yesnoj/FilMachine_Reworked/3D_Models/FilMachine_macchina_v5/png/bagno_e_idraulica.png

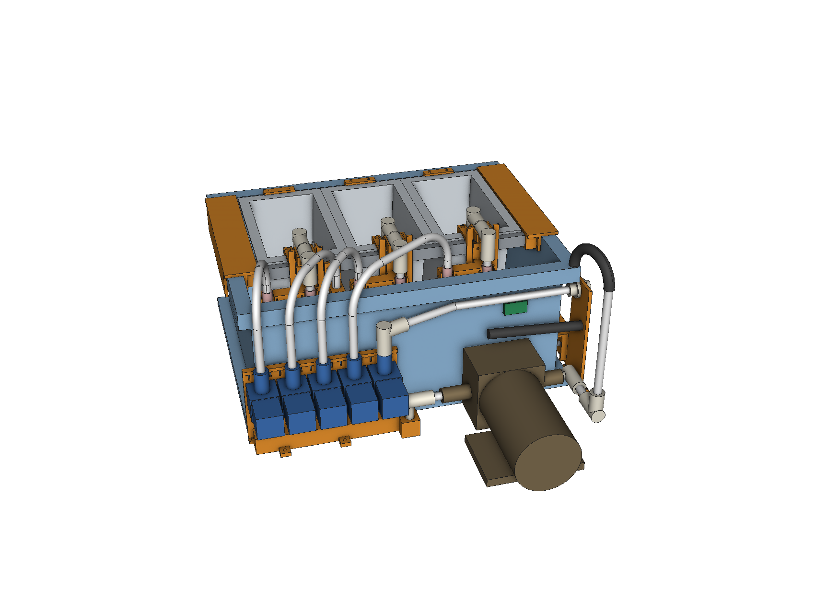
3D_Models/FilMachine_macchina_v5/png/bagno_e_idraulica.png
