yesnoj/FilMachine_Reworked/3D_Models/FilMachine_macchina_v5/png/culla_universale_135.png

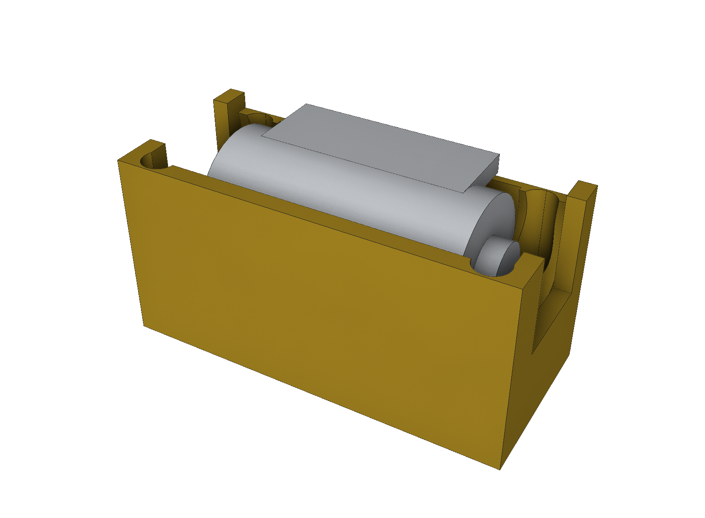
3D_Models/FilMachine_macchina_v5/png/culla_universale_135.png
