yesnoj/FilMachine_Reworked/3D_Models/FilMachine_macchina_v5/png/sez_macchina_tank.png

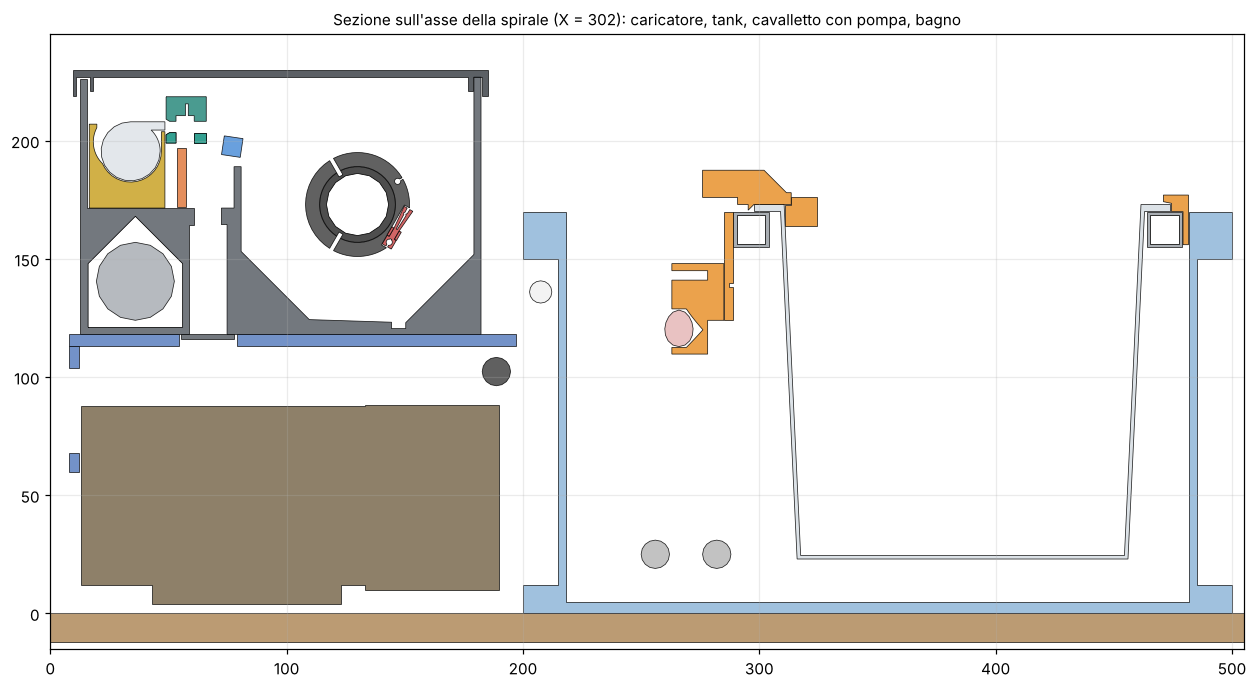
3D_Models/FilMachine_macchina_v5/png/sez_macchina_tank.png
