yesnoj/FilMachine_Reworked/3D_Models/FilMachine_macchina_v5/png/tank_trasmissione.png

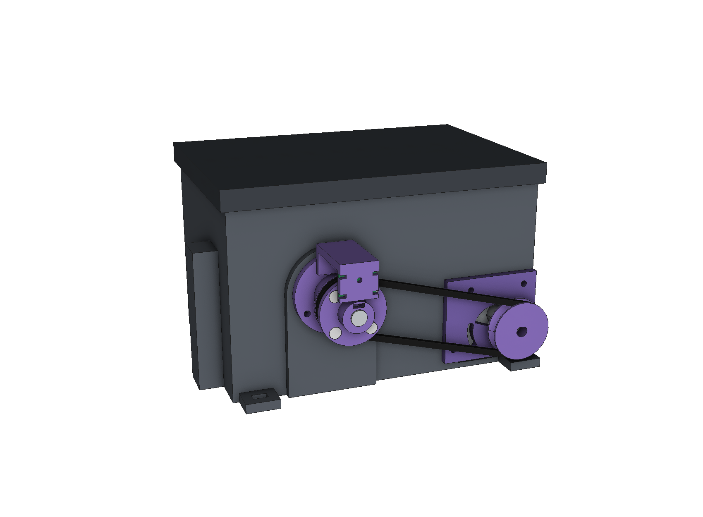
3D_Models/FilMachine_macchina_v5/png/tank_trasmissione.png
