yesnoj/FilMachine_Reworked/3D_Models/FilMachine_macchina_v5/step/B01_corpo_tank.step

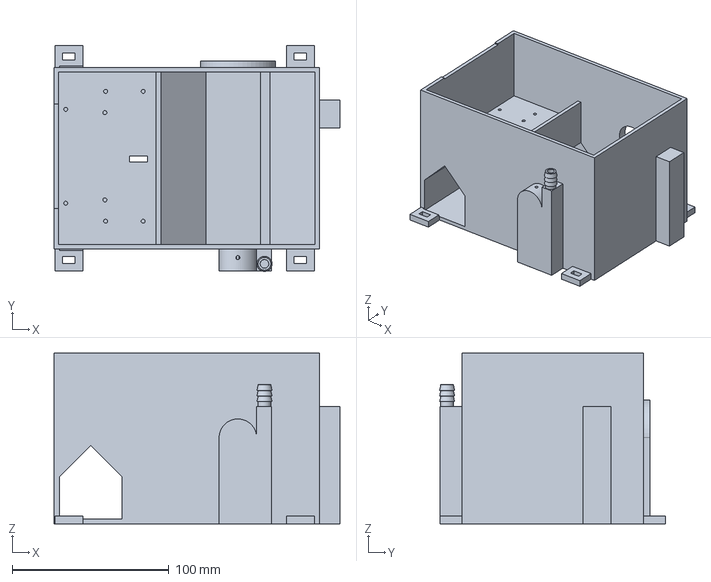
[picture p39: CAD file, 2026-10-09]
3D_Models/FilMachine_macchina_v5/step/B01_corpo_tank.step
182.8 x 144.3 x 109.0 mm
