yesnoj/FilMachine_Reworked/3D_Models/FilMachine_macchina_v5/step/B22_puleggia_motore.step

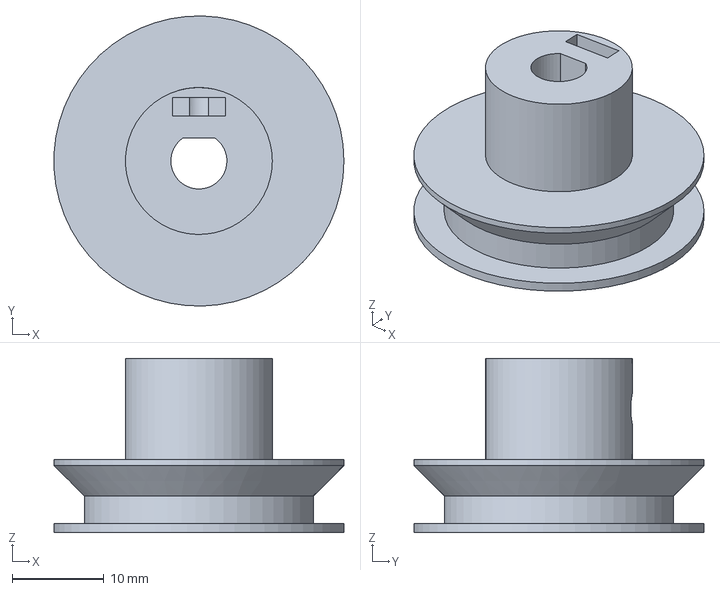
[picture p41: CAD file, 2026-10-09]
3D_Models/FilMachine_macchina_v5/step/B22_puleggia_motore.step
31.6 x 31.6 x 19.0 mm
