yesnoj/FilMachine_Reworked/3D_Models/FilMachine_macchina_v5/step/D11_paratia_posteriore.step

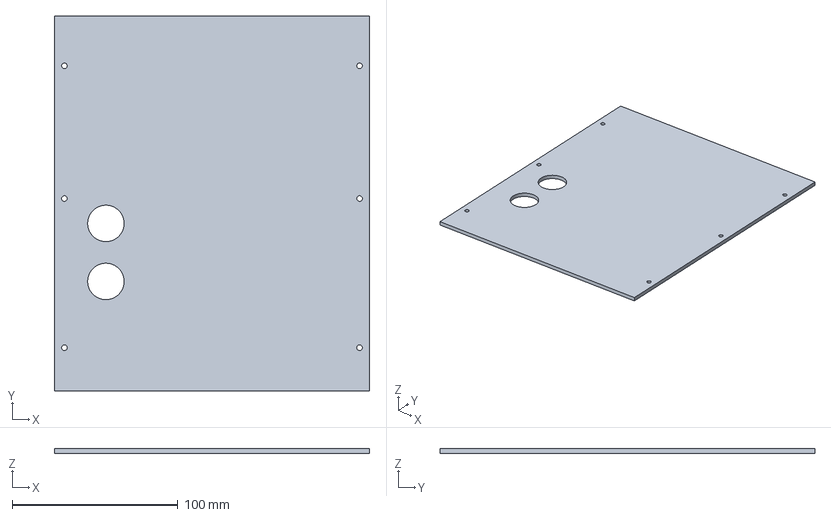
[picture p42: CAD file, 2026-10-09]
3D_Models/FilMachine_macchina_v5/step/D11_paratia_posteriore.step
190.0 x 226.0 x 3.00 mm
