yesnoj/FilMachine_Reworked/3D_Models/FilMachine_macchina_v5/step/D01_piano_cavalletto.step

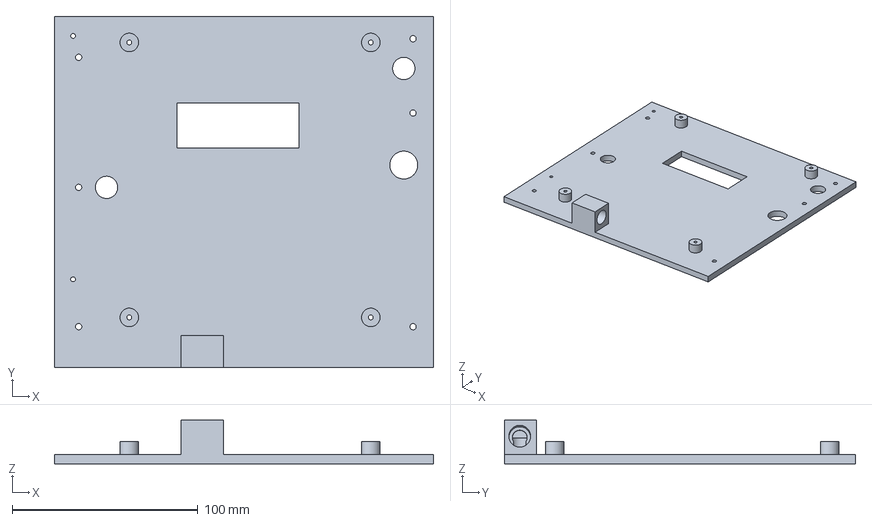
[picture p43: CAD file, 2026-10-09]
3D_Models/FilMachine_macchina_v5/step/D01_piano_cavalletto.step
204.0 x 189.0 x 23.5 mm
