yesnoj/FilMachine_Reworked/3D_Models/FilMachine_macchina_v5/step/A08_clip_cursore.step

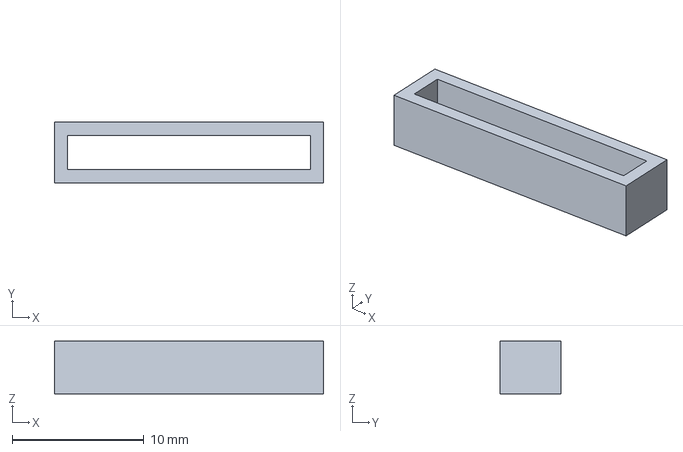
[picture p44: CAD file, 2026-10-09]
3D_Models/FilMachine_macchina_v5/step/A08_clip_cursore.step
20.4 x 4.60 x 4.00 mm
