yesnoj/FilMachine_Reworked/3D_Models/FilMachine_macchina_v5/step/C01_sella_testina.step

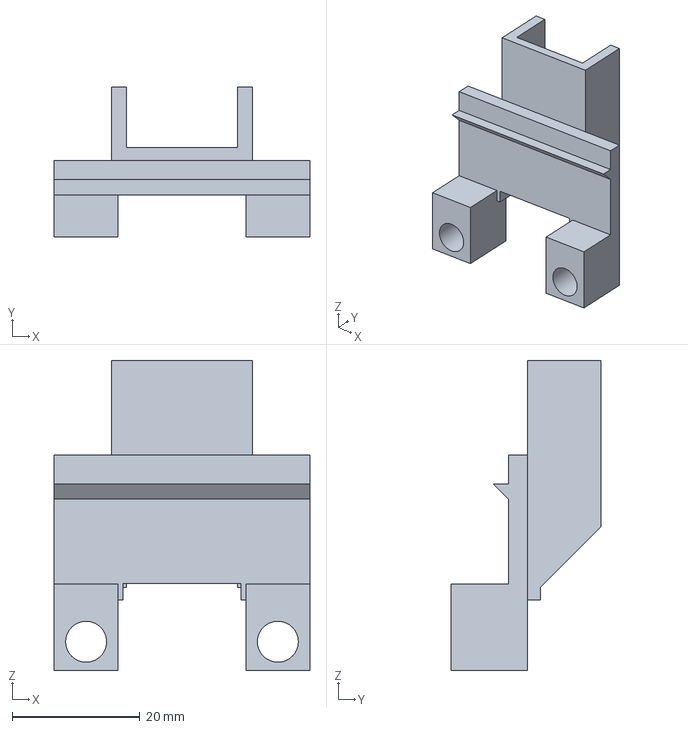
[picture p45: CAD file, 2026-10-09]
3D_Models/FilMachine_macchina_v5/step/C01_sella_testina.step
40.0 x 23.5 x 48.5 mm
