yesnoj/FilMachine_Reworked/3D_Models/FilMachine_macchina_v5/step/D14_colonnina_alta.step

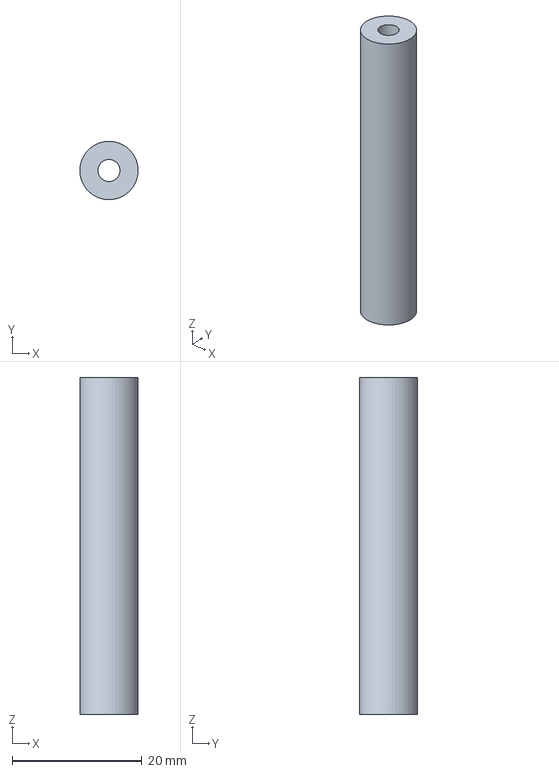
[picture p46: CAD file, 2026-10-09]
3D_Models/FilMachine_macchina_v5/step/D14_colonnina_alta.step
8.99 x 9.00 x 52.0 mm
