yesnoj/FilMachine_Reworked/3D_Models/FilMachine_macchina_v5/step/D03_fianco_cavalletto_DX.step

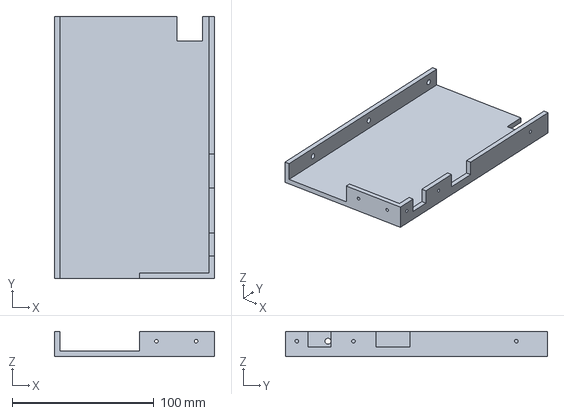
[picture p47: CAD file, 2026-10-09]
3D_Models/FilMachine_macchina_v5/step/D03_fianco_cavalletto_DX.step
113.0 x 185.0 x 18.0 mm
