yesnoj/FilMachine_Reworked/3D_Models/FilMachine_macchina_v5/step/B25_staffa_hall.step

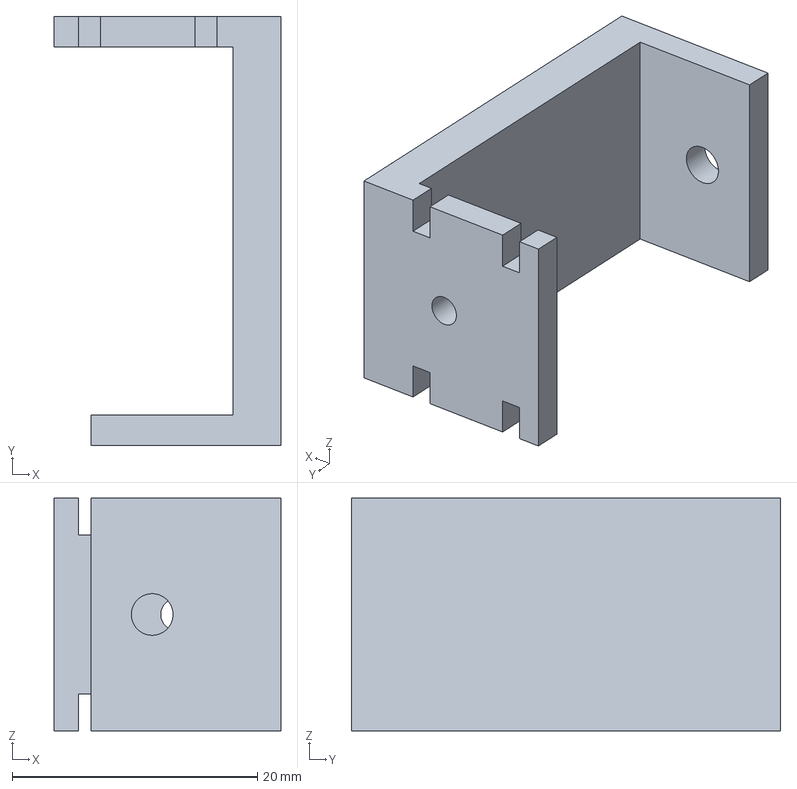
[picture p48: CAD file, 2026-10-09]
3D_Models/FilMachine_macchina_v5/step/B25_staffa_hall.step
18.5 x 35.0 x 19.0 mm
