yesnoj/FilMachine_Reworked/3D_Models/FilMachine_macchina_v5/step/A07_clip_ganascia.step

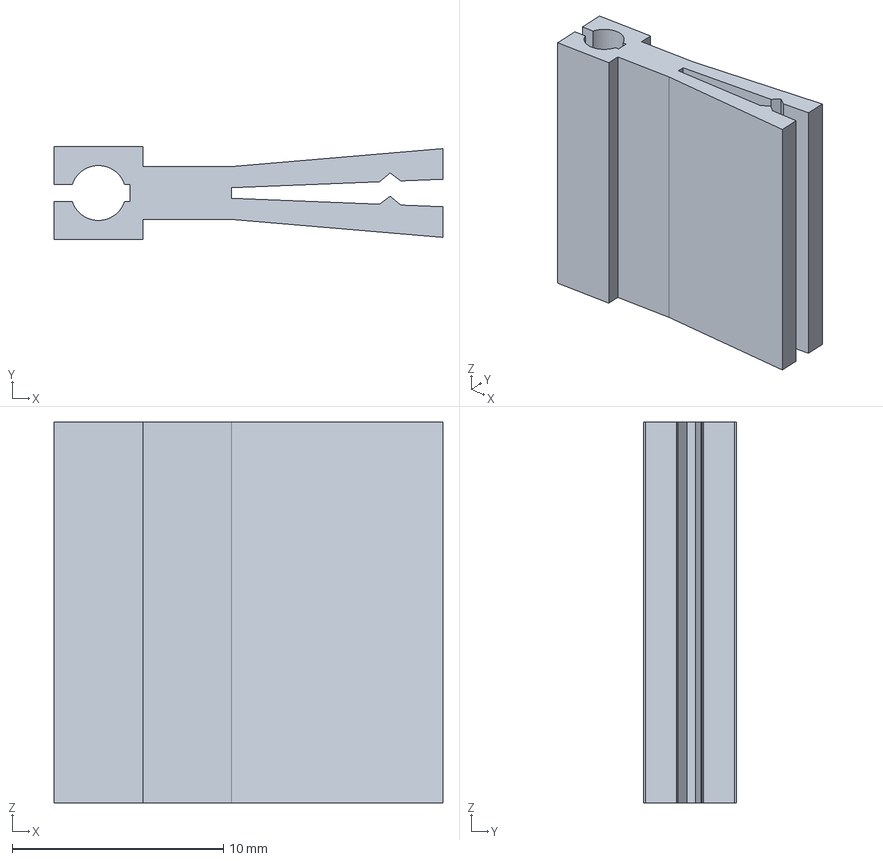
[picture p49: CAD file, 2026-10-09]
3D_Models/FilMachine_macchina_v5/step/A07_clip_ganascia.step
18.4 x 4.40 x 18.0 mm
