yesnoj/FilMachine_Reworked/3D_Models/FilMachine_macchina_v5/step/C02_culla_sifone.step

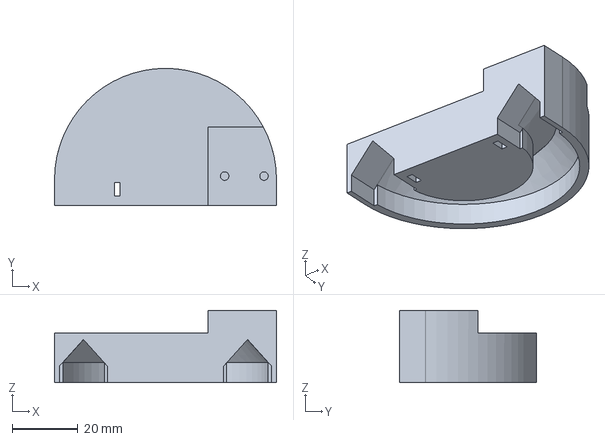
[picture p50: CAD file, 2026-10-09]
3D_Models/FilMachine_macchina_v5/step/C02_culla_sifone.step
67.6 x 41.8 x 22.0 mm
