yesnoj/FilMachine_Reworked/3D_Models/FilMachine_macchina_v5/step/B08_morsetto_lama_DX.step

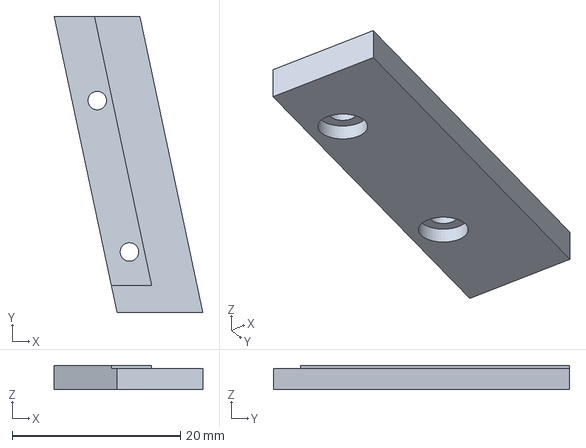
[picture p51: CAD file, 2026-10-09]
3D_Models/FilMachine_macchina_v5/step/B08_morsetto_lama_DX.step
17.7 x 35.2 x 2.88 mm
