yesnoj/FilMachine_Reworked/3D_Models/FilMachine_macchina_v5/step/D04_frontale_cavalletto.step

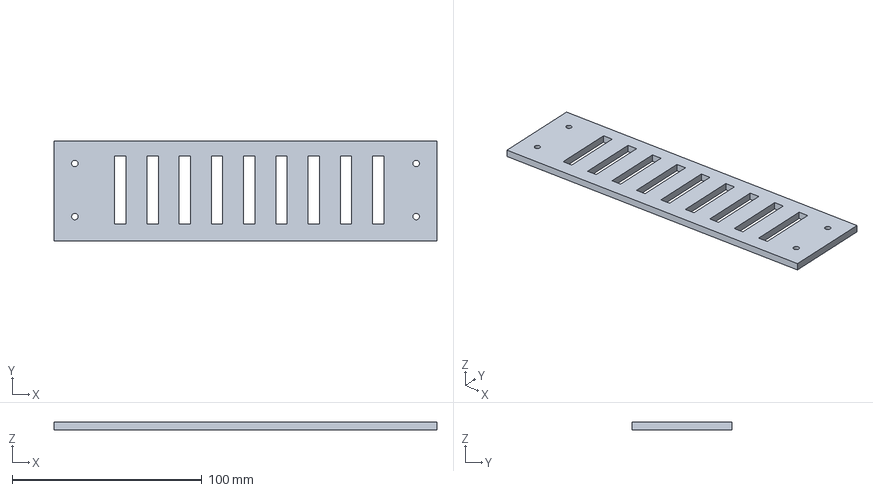
[picture p52: CAD file, 2026-10-09]
3D_Models/FilMachine_macchina_v5/step/D04_frontale_cavalletto.step
202.0 x 53.0 x 4.00 mm
