yesnoj/FilMachine_Reworked/3D_Models/FilMachine_macchina_v5/step/B24_perno_folle.step

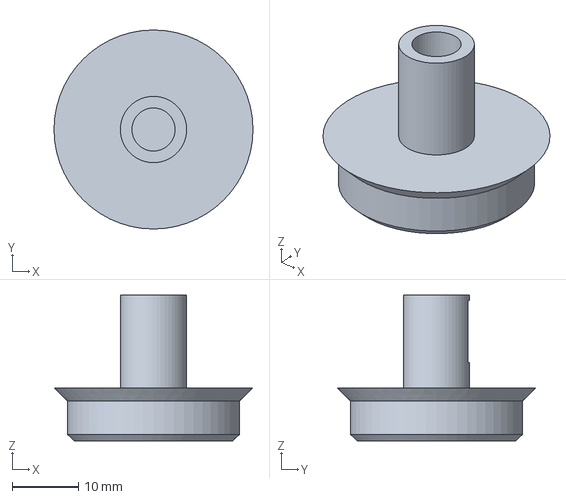
[picture p53: CAD file, 2026-10-09]
3D_Models/FilMachine_macchina_v5/step/B24_perno_folle.step
30.0 x 30.0 x 22.0 mm
