yesnoj/FilMachine_Reworked/3D_Models/FilMachine_macchina_v5/step/B18_distanziale_paraolio.step

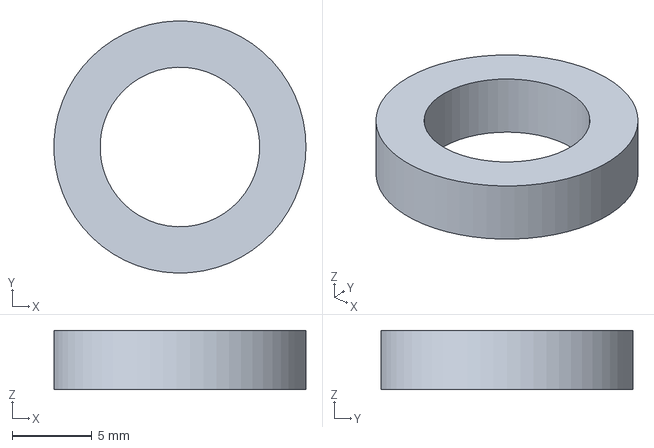
[picture p54: CAD file, 2026-10-09]
3D_Models/FilMachine_macchina_v5/step/B18_distanziale_paraolio.step
15.8 x 15.8 x 3.70 mm
