yesnoj/FilMachine_Reworked/3D_Models/FilMachine_macchina_v5/step/B17_cartuccia_cuscinetti.step

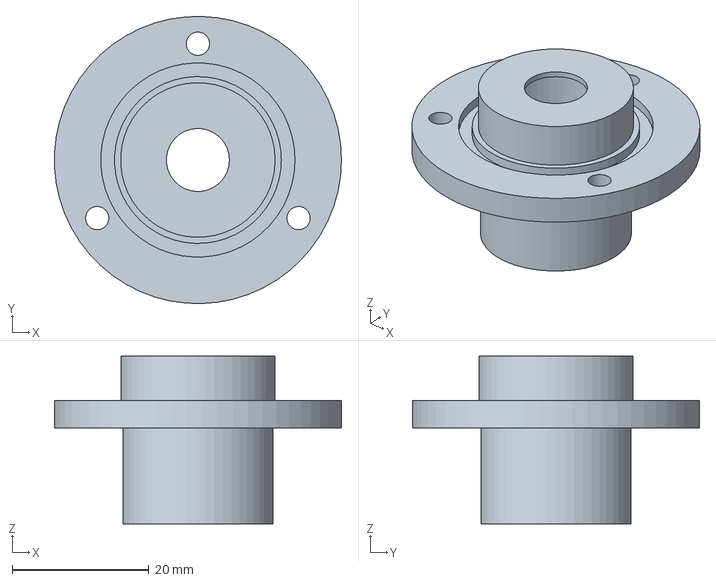
[picture p55: CAD file, 2026-10-09]
3D_Models/FilMachine_macchina_v5/step/B17_cartuccia_cuscinetti.step
42.0 x 42.0 x 24.5 mm
