yesnoj/FilMachine_Reworked/3D_Models/FilMachine_macchina_v5/step/B16_trascinatore.step

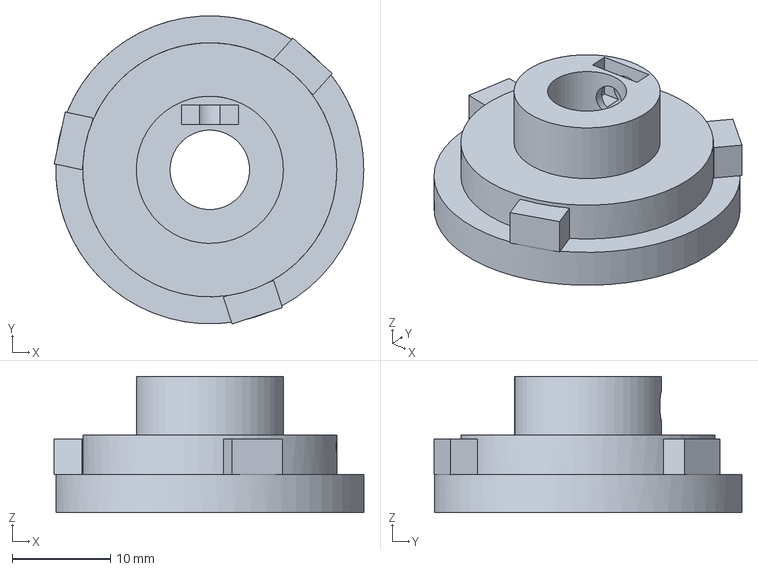
[picture p56: CAD file, 2026-10-09]
3D_Models/FilMachine_macchina_v5/step/B16_trascinatore.step
31.6 x 31.4 x 13.9 mm
