yesnoj/FilMachine_Reworked/3D_Models/FilMachine_macchina_v5/step/B23_piastra_motore.step

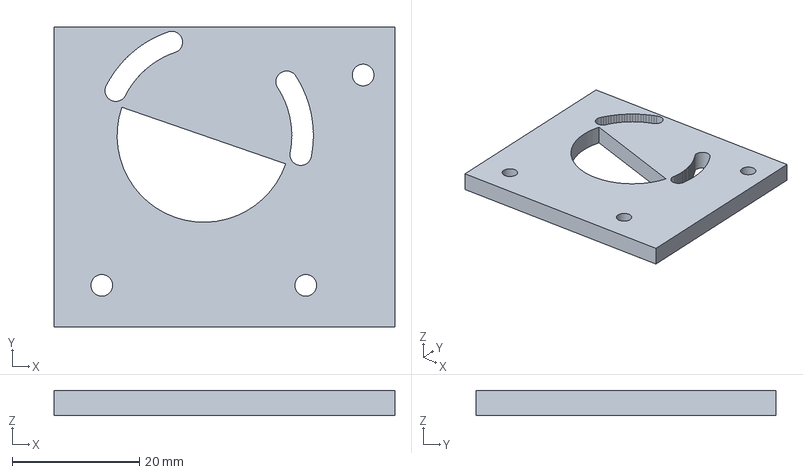
[picture p57: CAD file, 2026-10-09]
3D_Models/FilMachine_macchina_v5/step/B23_piastra_motore.step
53.5 x 47.0 x 4.00 mm
