yesnoj/FilMachine_Reworked/3D_Models/FilMachine_macchina_v5/step/B03_coperchietto_vano_servo.step

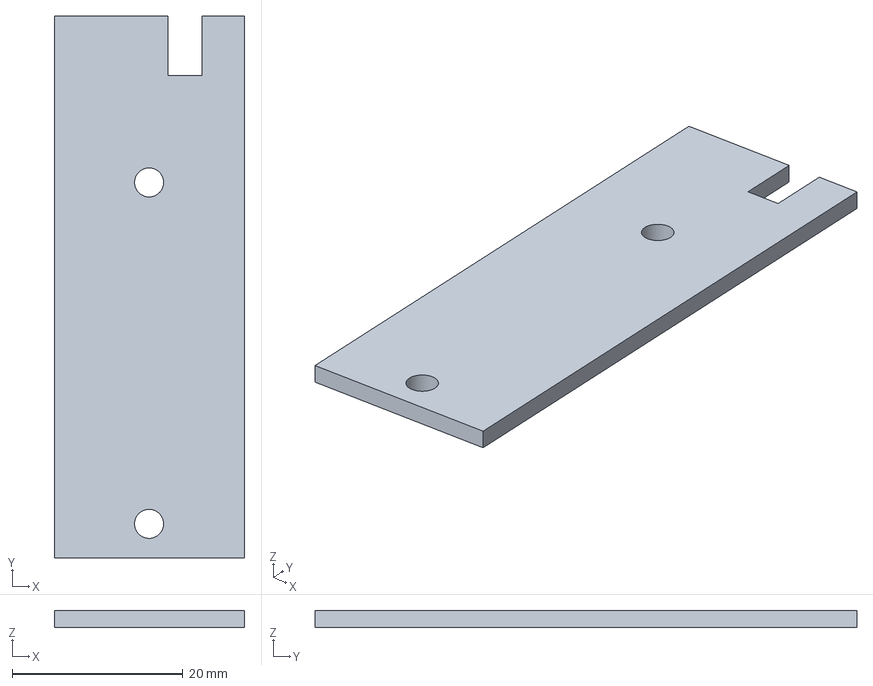
[picture p58: CAD file, 2026-10-09]
3D_Models/FilMachine_macchina_v5/step/B03_coperchietto_vano_servo.step
22.3 x 63.5 x 2.00 mm
