yesnoj/FilMachine_Reworked/3D_Models/FilMachine_macchina_v5/step/B13_barra_guida.step

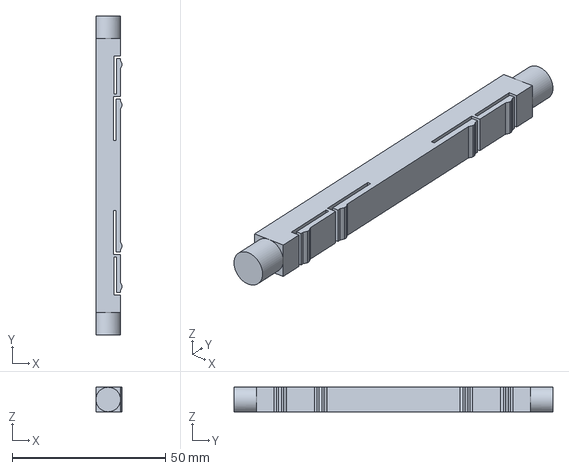
[picture p59: CAD file, 2026-10-09]
3D_Models/FilMachine_macchina_v5/step/B13_barra_guida.step
8.50 x 104.0 x 8.00 mm
