yesnoj/FilMachine_Reworked/3D_Models/FilMachine_macchina_v5/step/A04_tamburo.step

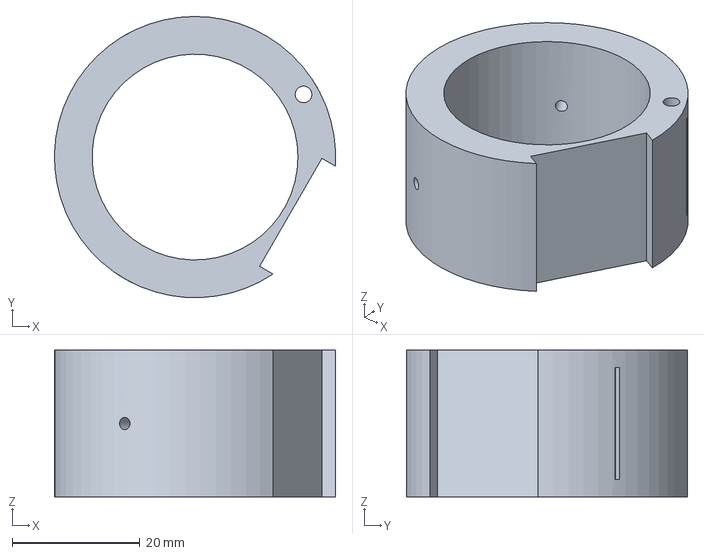
[picture p60: CAD file, 2026-10-09]
3D_Models/FilMachine_macchina_v5/step/A04_tamburo.step
44.0 x 44.0 x 23.0 mm
