yesnoj/FilMachine_Reworked/3D_Models/FilMachine_macchina_v5/step/B15_slitta_SX.step

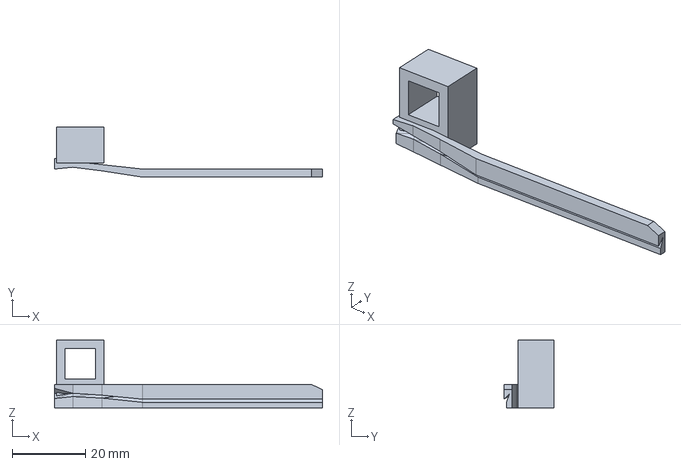
[picture p61: CAD file, 2026-10-09]
3D_Models/FilMachine_macchina_v5/step/B15_slitta_SX.step
73.0 x 13.7 x 18.5 mm
