yesnoj/FilMachine_Reworked/3D_Models/FilMachine_macchina_v5/step/B12_culla_universale.step

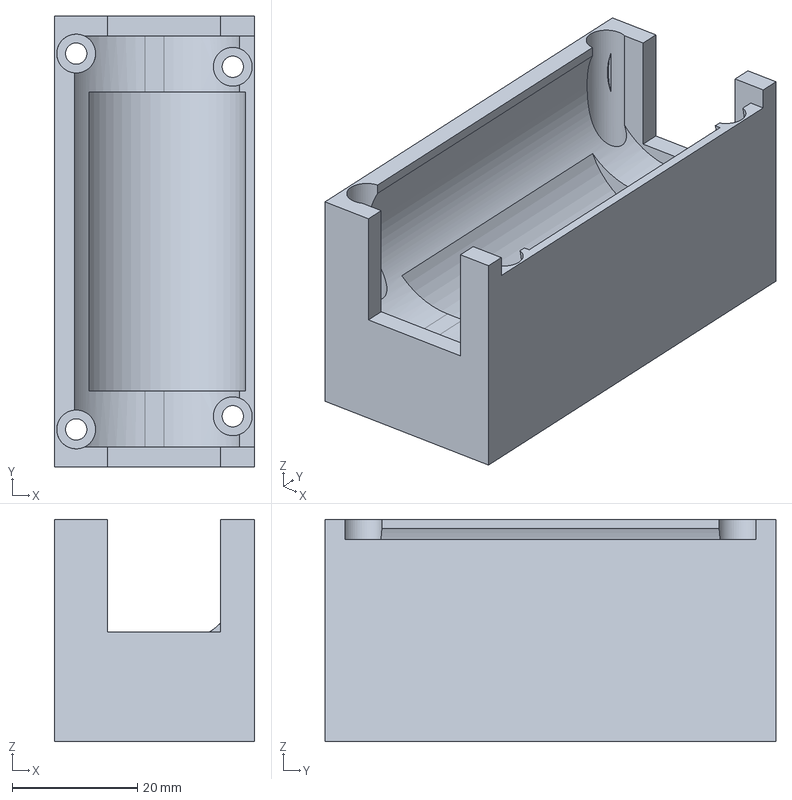
[picture p62: CAD file, 2026-10-09]
3D_Models/FilMachine_macchina_v5/step/B12_culla_universale.step
32.0 x 72.0 x 35.5 mm
