yesnoj/FilMachine_Reworked/3D_Models/FilMachine_macchina_v5/step/B19_distanziale_cuscinetti.step

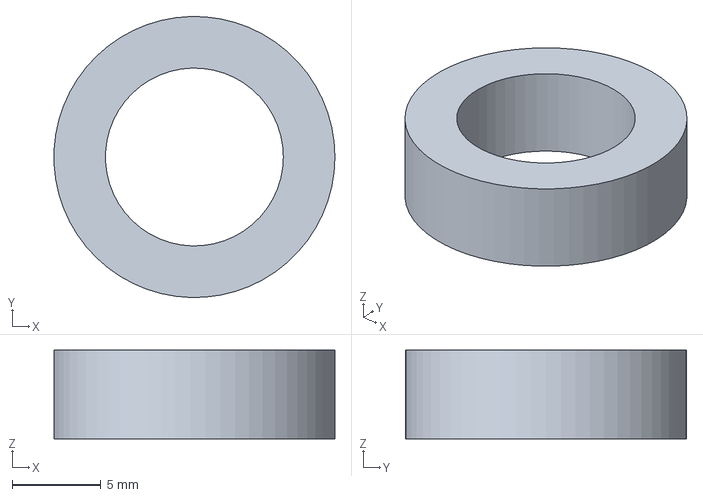
[picture p63: CAD file, 2026-10-09]
3D_Models/FilMachine_macchina_v5/step/B19_distanziale_cuscinetti.step
15.8 x 15.8 x 5.00 mm
