yesnoj/FilMachine_Reworked/3D_Models/FilMachine_macchina_v5/step/D12_ripiano_griglia.step

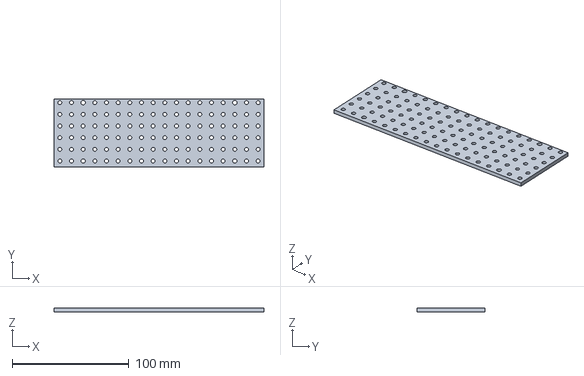
[picture p64: CAD file, 2026-10-09]
3D_Models/FilMachine_macchina_v5/step/D12_ripiano_griglia.step
180.0 x 58.0 x 3.00 mm
