yesnoj/FilMachine_Reworked/3D_Models/FilMachine_macchina_v5/step/C06_portasonde.step

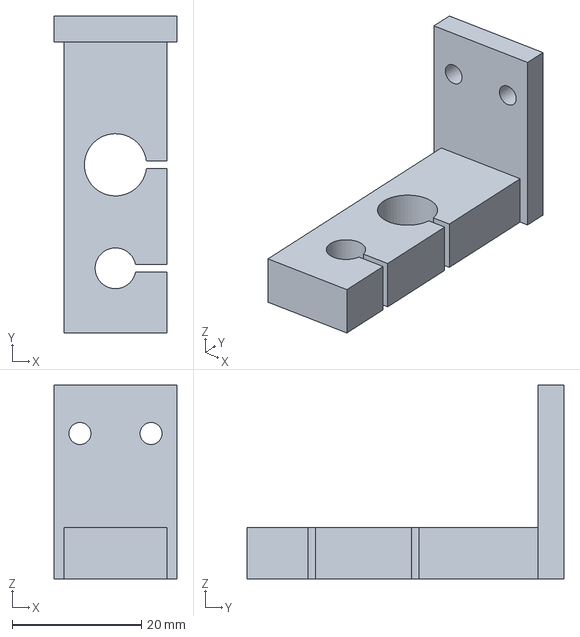
[picture p65: CAD file, 2026-10-09]
3D_Models/FilMachine_macchina_v5/step/C06_portasonde.step
19.0 x 49.0 x 30.0 mm
