yesnoj/FilMachine_Reworked/3D_Models/FilMachine_macchina_v5/step/B20_rasamento_puleggia.step

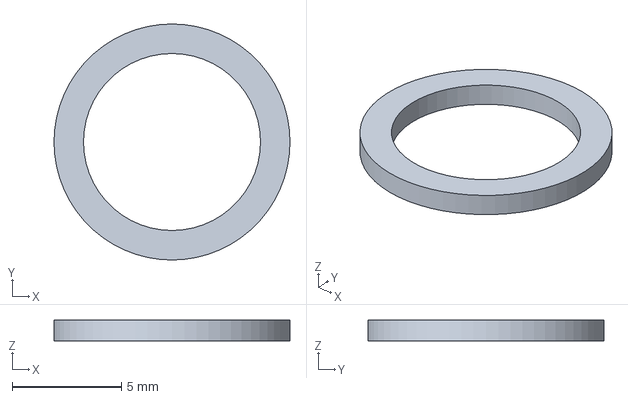
[picture p66: CAD file, 2026-10-09]
3D_Models/FilMachine_macchina_v5/step/B20_rasamento_puleggia.step
10.8 x 10.8 x 0.95 mm
