yesnoj/FilMachine_Reworked/3D_Models/FilMachine_macchina_v5/step/D07_fianco_elettronica_DX.step

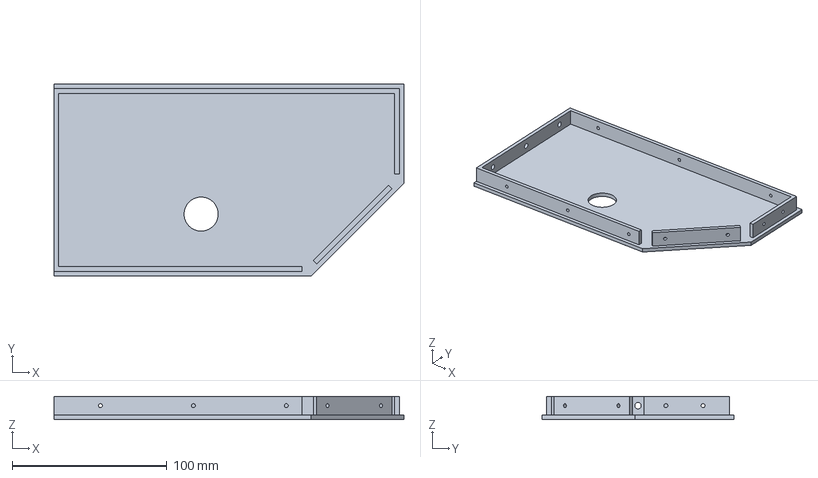
[picture p67: CAD file, 2026-10-09]
3D_Models/FilMachine_macchina_v5/step/D07_fianco_elettronica_DX.step
226.0 x 124.0 x 15.0 mm
