yesnoj/FilMachine_Reworked/3D_Models/FilMachine_macchina_v5/step/C09_staffa_scarichi.step

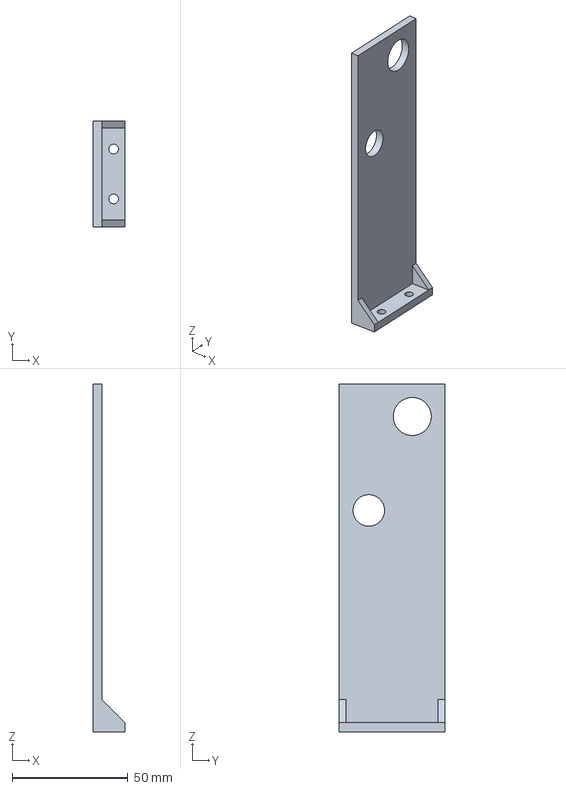
[picture p68: CAD file, 2026-10-09]
3D_Models/FilMachine_macchina_v5/step/C09_staffa_scarichi.step
14.0 x 45.5 x 150.0 mm
