yesnoj/FilMachine_Reworked/3D_Models/FilMachine_macchina_v5/step/C07_collettore.step

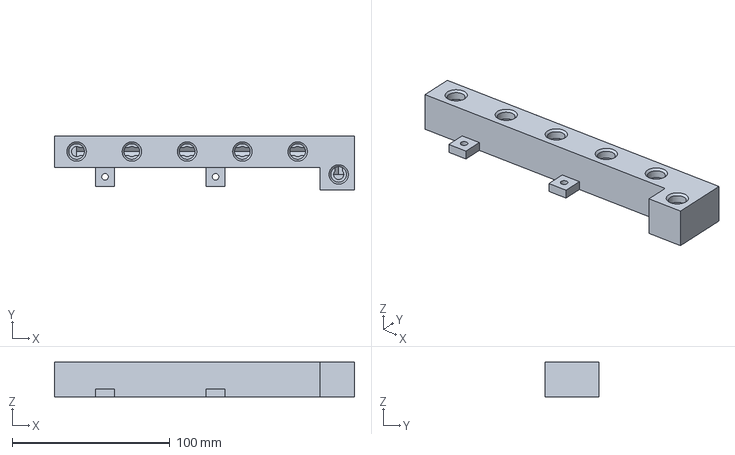
[picture p69: CAD file, 2026-10-09]
3D_Models/FilMachine_macchina_v5/step/C07_collettore.step
190.0 x 34.5 x 22.0 mm
