yesnoj/FilMachine_Reworked/3D_Models/FilMachine_macchina_v5/step/D13_colonnina_bassa.step

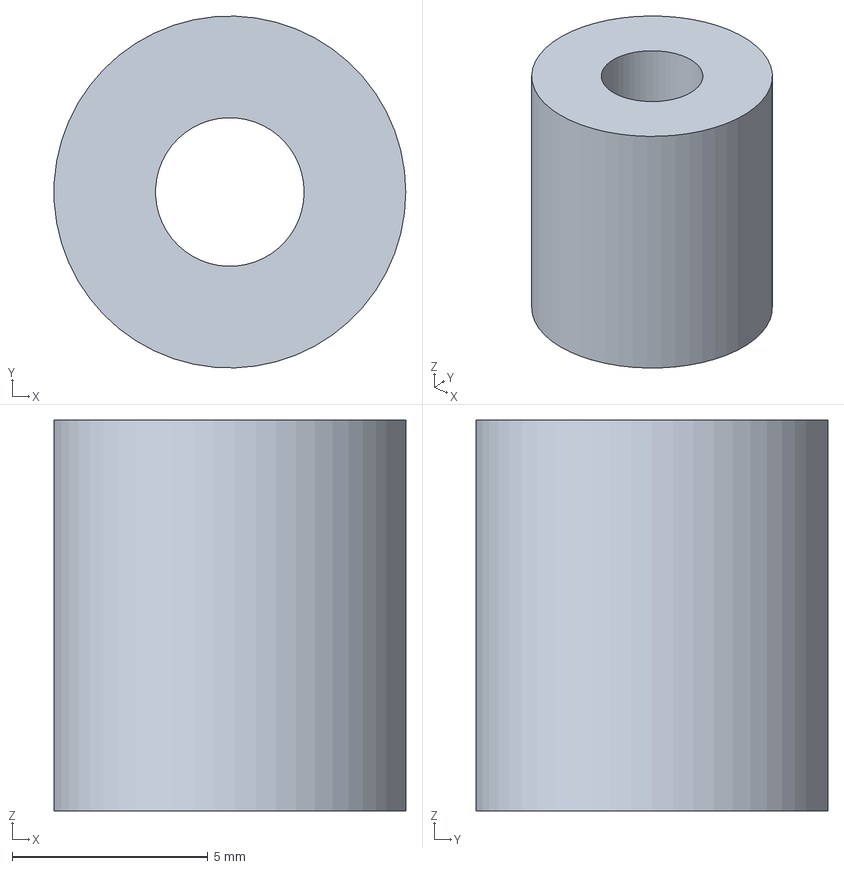
[picture p70: CAD file, 2026-10-09]
3D_Models/FilMachine_macchina_v5/step/D13_colonnina_bassa.step
8.99 x 9.00 x 10.0 mm
