yesnoj/FilMachine_Reworked/3D_Models/FilMachine_macchina_v5/step/D15_morsetto_scheda.step

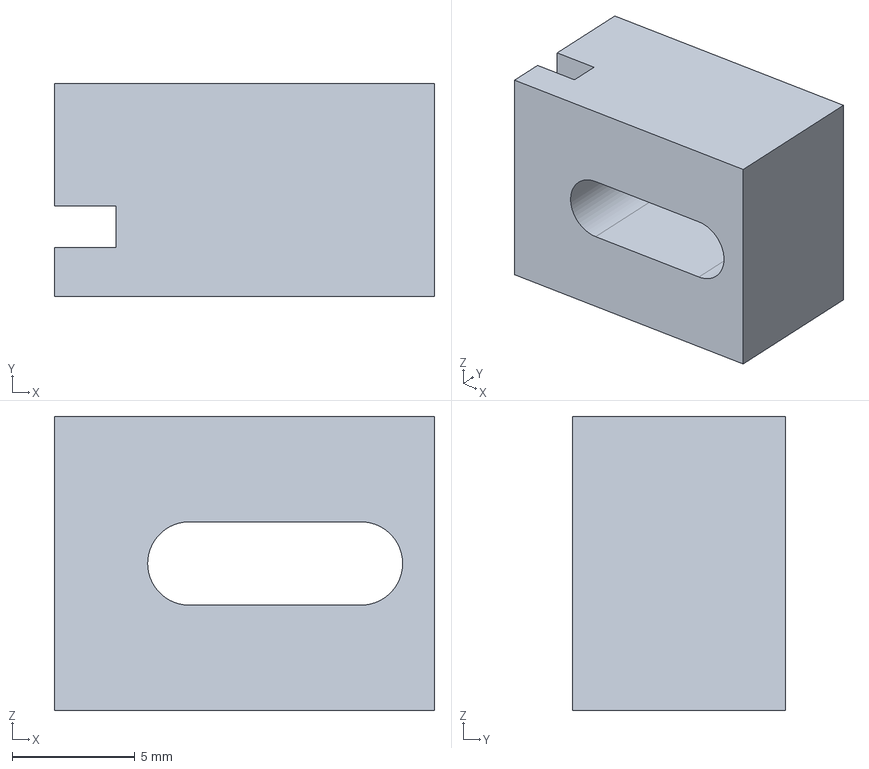
[picture p71: CAD file, 2026-10-09]
3D_Models/FilMachine_macchina_v5/step/D15_morsetto_scheda.step
15.5 x 8.70 x 12.0 mm
