yesnoj/FilMachine_Reworked/3D_Models/FilMachine_macchina_v5/step/C04_fermo_posteriore.step

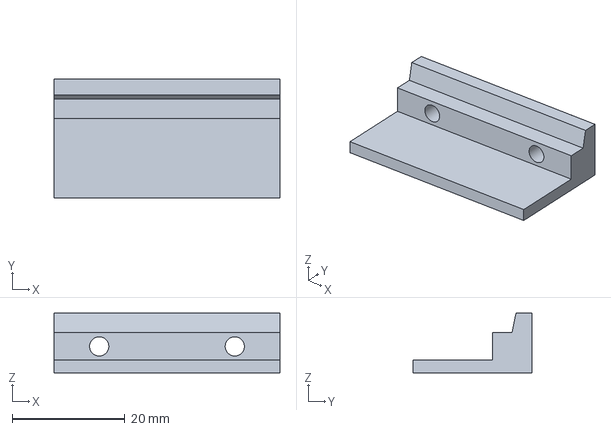
[picture p72: CAD file, 2026-10-09]
3D_Models/FilMachine_macchina_v5/step/C04_fermo_posteriore.step
40.0 x 21.0 x 10.6 mm
