yesnoj/FilMachine_Reworked/3D_Models/FilMachine_macchina_v5/step/C08_pettine_valvole.step

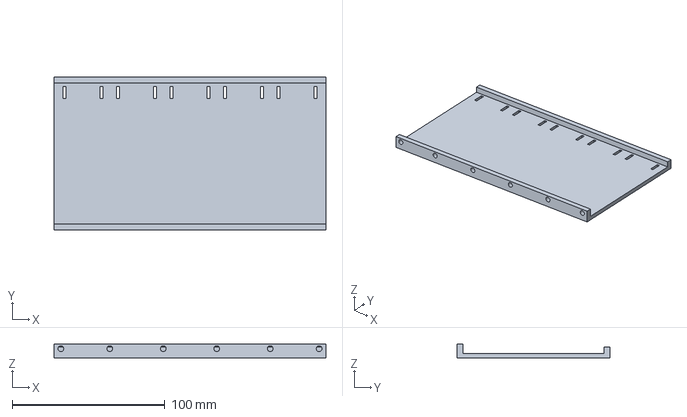
[picture p73: CAD file, 2026-10-09]
3D_Models/FilMachine_macchina_v5/step/C08_pettine_valvole.step
178.0 x 100.0 x 9.10 mm
