yesnoj/FilMachine_Reworked/3D_Models/FilMachine_macchina_v5/step/D17_linguetta_display.step

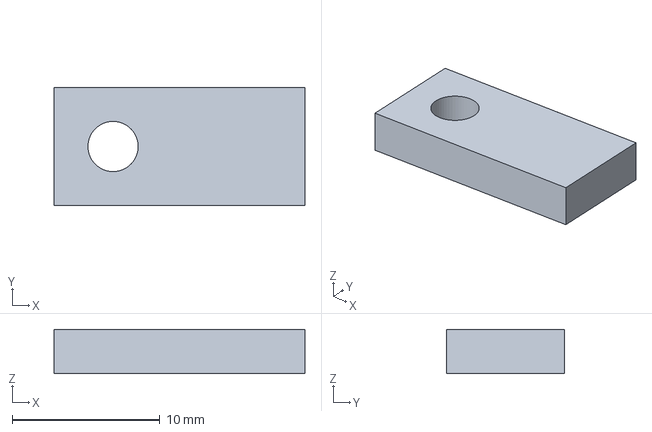
[picture p74: CAD file, 2026-10-09]
3D_Models/FilMachine_macchina_v5/step/D17_linguetta_display.step
17.0 x 8.00 x 3.00 mm
