yesnoj/FilMachine_Reworked/3D_Models/FilMachine_macchina_v5/step/A09_provino_accoppiamento.step

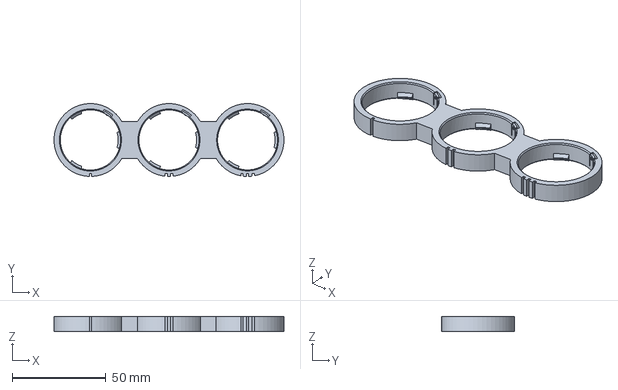
[picture p75: CAD file, 2026-10-09]
3D_Models/FilMachine_macchina_v5/step/A09_provino_accoppiamento.step
123.0 x 39.0 x 8.00 mm
