yesnoj/FilMachine_Reworked/3D_Models/FilMachine_macchina_v5/step/C03_staffa_ganci.step

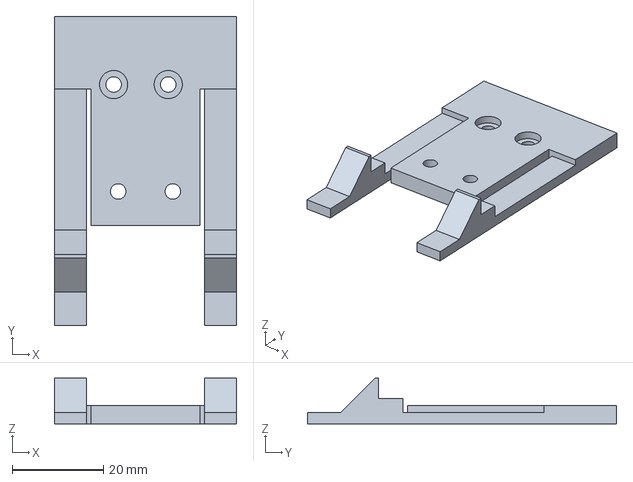
[picture p76: CAD file, 2026-10-09]
3D_Models/FilMachine_macchina_v5/step/C03_staffa_ganci.step
40.0 x 68.0 x 10.0 mm
