yesnoj/FilMachine_Reworked/3D_Models/FilMachine_macchina_v5/step/D09_plancia_display.step

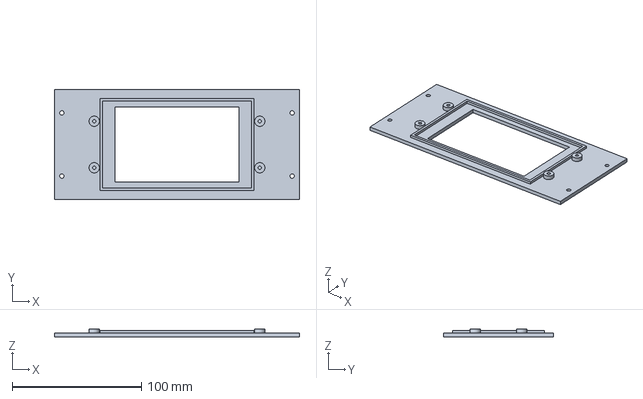
[picture p77: CAD file, 2026-10-09]
3D_Models/FilMachine_macchina_v5/step/D09_plancia_display.step
189.4 x 84.9 x 6.20 mm
