yesnoj/FilMachine_Reworked/3D_Models/FilMachine_macchina_v5/step/B21_puleggia_spirale.step

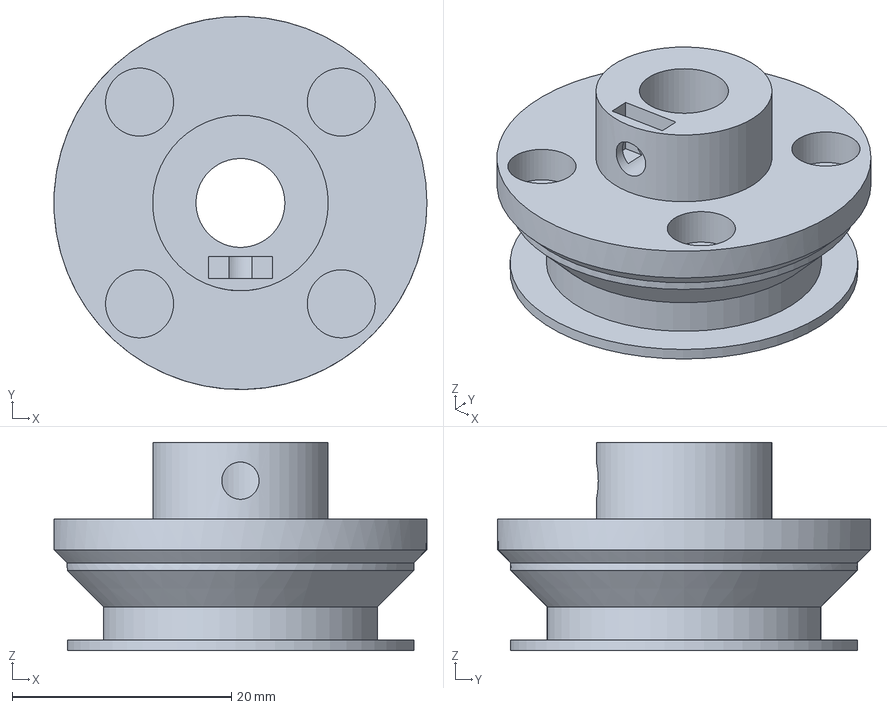
[picture p78: CAD file, 2026-10-09]
3D_Models/FilMachine_macchina_v5/step/B21_puleggia_spirale.step
34.0 x 34.0 x 19.0 mm
