yesnoj/FilMachine_Reworked/3D_Models/FilMachine_macchina_v5/step/B10_biella.step

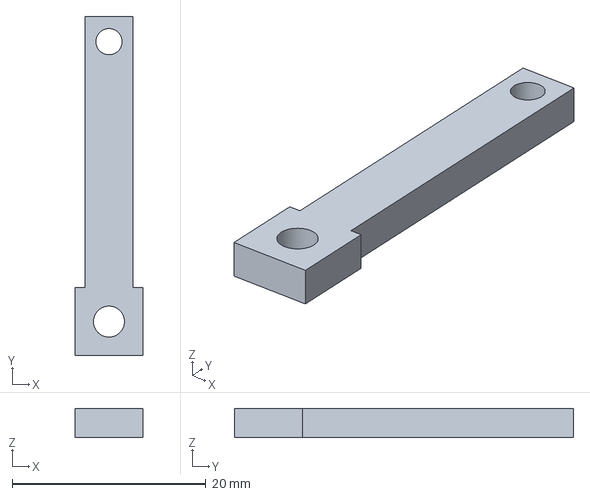
[picture p79: CAD file, 2026-10-09]
3D_Models/FilMachine_macchina_v5/step/B10_biella.step
7.00 x 35.0 x 3.00 mm
