yesnoj/FilMachine_Reworked/3D_Models/FilMachine_macchina_v5/step/D10_tetto_elettronica.step

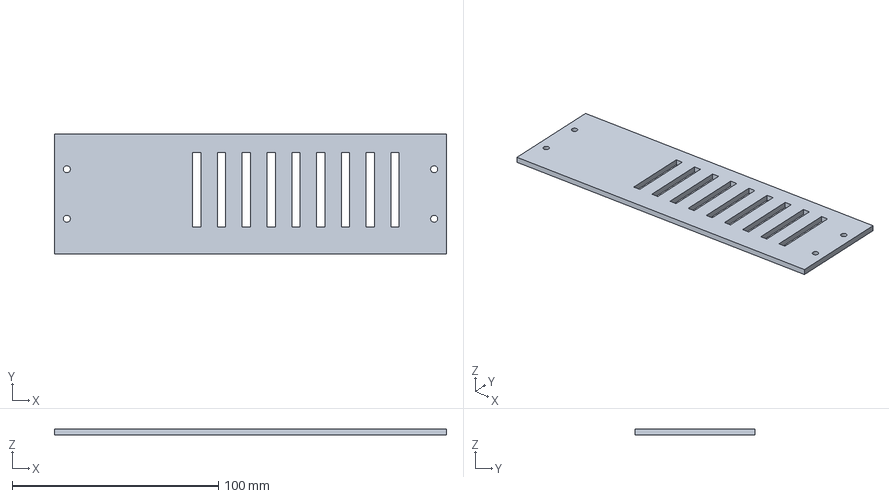
[picture p80: CAD file, 2026-10-09]
3D_Models/FilMachine_macchina_v5/step/D10_tetto_elettronica.step
190.0 x 58.0 x 3.00 mm
