yesnoj/FilMachine_Reworked/hardware/FilMachine_Breakout_v1/FilMachine_Breakout_v1.kicad_sch

## KiCad design hardware/FilMachine_Breakout_v1/FilMachine_Breakout_v1.kicad_sch (2026-05-02)

Schematic: FilMachine_Breakout_v1.kicad_sch

Parts:
C1, C2: 100nF; C_0805_2012Metric
J1: J9_Expand_IO_2x13; PinHeader_2x13_P2.54mm_Vertical
J2: MOTOR_3P_5.08mm; TerminalBlock_bornier-3_P5.08mm
J3: TEMP_3P_5.08mm; TerminalBlock_bornier-3_P5.08mm
J4: FLOW_3P_5.08mm; TerminalBlock_bornier-3_P5.08mm
J5: I2C_4P_5.08mm; TerminalBlock_bornier-4_P5.08mm
J6: WATER_4P_5.08mm; TerminalBlock_bornier-4_P5.08mm
J7: HALL_3P_5.08mm; TerminalBlock_bornier-3_P5.08mm
J8: SPARE_GPIO_1x8; PinHeader_1x08_P2.54mm_Vertical
J9: PWR_5V_3V3_GND; TerminalBlock_bornier-4_P5.08mm
R1, R2, R3: 4.7k; R_0805_2012Metric

Notes on the sheet:
FilMachine Breakout Board v1.0 J9 Expand IO → Screw Terminals + Passives
