yesnoj/FilMachine_Reworked/main/accessories.c

/*
 * FilMachine_support.c
 *
 *  Created on: 2 May 2025
 *      Author: PeterB
 */
#include <ctype.h>
#include <string.h>
#include <stdlib.h>
#include <sys/unistd.h>
#include <sys/stat.h>

#include "driver/sdmmc_host.h"
#if defined(BOARD_JC4880P433)
    #include "sd_pwr_ctrl_by_on_chip_ldo.h"
#endif
#include "esp_err.h"
#include "esp_log.h"
#include "ff.h"
#include "sdmmc_cmd.h"
#if defined(BOARD_JC4880P433)
    #include "driver/i2c_master.h"
#else
    #include "driver/i2c.h"
#endif
#include "driver/gpio.h"
#include "driver/ledc.h"
#include "esp_vfs_fat.h"
#include "esp_heap_caps.h"
#ifndef SIMULATOR_BUILD
#include "audio.h"
#include "nvs.h"
#endif
#include "sensors.h"
#include "sd_log.h"

#include "FilMachine.h"
#include "ws_server.h"
#include "mcp23017.h"
#include "ds18b20.h"
#include "mini_json.h"
/* pca9685.h removed — pump now driven by DBH-12V H-bridge */

#define LESS_THAN_10 1
#define GREATER_THAN_9 2
#define GREATER_THAN_99 3

extern struct gui_components		gui;
extern struct sys_components		sys;
extern uint8_t						initErrors;

static const char			*TAG = "Accessory"; /* ESP Debug Message Tag */
static mcp23017_t           mcp;                /* MCP23017 I/O expander handle */
static ds18b20_bus_t        ds_bus;             /* DS18B20 shared OneWire bus (both sensors) */
/* PCA9685 removed — pump speed now via LEDC on DBH-12V H-bridge channel B */

static void process_list_set_time_label(processNode *process);

/* ═══════════════════════════════════════════════
 * Utility Helpers
 * ═══════════════════════════════════════════════ */

/** Round a value to the nearest step (e.g., roundToStep(77, 10) → 80) */
int32_t roundToStep(int32_t value, int32_t step) {
    int32_t remainder = value % step;
    if (remainder == 0) return value;
    return (remainder > step / 2) ? value + (step - remainder) : value - remainder;
}

/** Safely delete an LVGL timer and null-out the pointer */
/* Result of the last export (Tools → Export), read by the app through the
 * state broadcast: exportSeq changes after every attempt. */
volatile uint16_t g_exportSeq = 0;
volatile bool     g_exportOk  = false;

bool maintenanceBusy(void) {
    return machineFillState() == FILL_RUNNING || filmLoaderBusy() || drainToolBusy() || cleanToolBusy();
}

void safeTimerDelete(lv_timer_t **timer) {
    if (timer != NULL && *timer != NULL) {
        lv_timer_delete(*timer);
        *timer = NULL;
    }
}

/* LEDC PWM for motor ENA pin */
#define MOTOR_LEDC_TIMER      LEDC_TIMER_0
#define MOTOR_LEDC_MODE       LEDC_LOW_SPEED_MODE
#define MOTOR_LEDC_CHANNEL    LEDC_CHANNEL_0
#define MOTOR_LEDC_FREQ_HZ    5000
#define MOTOR_LEDC_RESOLUTION  LEDC_TIMER_8_BIT

static void motor_ledc_set_duty(uint8_t duty)
{
    ledc_set_duty(MOTOR_LEDC_MODE, MOTOR_LEDC_CHANNEL, duty);
    ledc_update_duty(MOTOR_LEDC_MODE, MOTOR_LEDC_CHANNEL);
}

/* ═══════════════════════════════════════════════
 * Pump H-bridge control (DBH-12V channel B)
 *
 * Uses LEDC timer 2 / channel 2.
 * Timer 0 / Channel 0 = agitation motor, Timer 1 / Channel 1 = backlight.
 * Same control scheme as the agitation motor:
 *   IN1=HIGH, IN2=LOW + ENA=PWM  → forward  (filling)
 *   IN1=LOW,  IN2=HIGH + ENA=PWM → reverse  (draining)
 * ═══════════════════════════════════════════════ */
#ifndef BOARD_SIMULATOR
#define PUMP_LEDC_TIMER       LEDC_TIMER_2       /* Timer 1 / Channel 1 = backlight! */
#define PUMP_LEDC_MODE        LEDC_LOW_SPEED_MODE
#define PUMP_LEDC_CHANNEL     LEDC_CHANNEL_2     /* Channel 1 = backlight! */
#define PUMP_LEDC_FREQ_HZ     16000           /* 16 kHz — recommended for normal DC motors */
#define PUMP_LEDC_RESOLUTION  LEDC_TIMER_8_BIT

static void pump_ledc_init(void)
{
    ledc_timer_config_t timer_cfg = {
        .speed_mode      = PUMP_LEDC_MODE,
        .timer_num        = PUMP_LEDC_TIMER,
        .duty_resolution  = PUMP_LEDC_RESOLUTION,
        .freq_hz          = PUMP_LEDC_FREQ_HZ,
        .clk_cfg          = LEDC_AUTO_CLK,
    };
    ESP_ERROR_CHECK(ledc_timer_config(&timer_cfg));

    ledc_channel_config_t ch_cfg = {
        .speed_mode = PUMP_LEDC_MODE,
        .channel    = PUMP_LEDC_CHANNEL,
        .timer_sel  = PUMP_LEDC_TIMER,
        .intr_type  = LEDC_INTR_DISABLE,
        .gpio_num   = PUMP_ENA_PIN,
        .duty       = 0,
        .hpoint     = 0,
    };
    ESP_ERROR_CHECK(ledc_channel_config(&ch_cfg));

    /* Direction pins as GPIO output */
    gpio_config_t io_conf = {
        .pin_bit_mask = (1ULL << PUMP_IN1_PIN) | (1ULL << PUMP_IN2_PIN),
        .mode         = GPIO_MODE_OUTPUT,
        .pull_up_en   = GPIO_PULLUP_DISABLE,
        .pull_down_en = GPIO_PULLDOWN_DISABLE,
        .intr_type    = GPIO_INTR_DISABLE,
    };
    ESP_ERROR_CHECK(gpio_config(&io_conf));
    gpio_set_level(PUMP_IN1_PIN, 0);
    gpio_set_level(PUMP_IN2_PIN, 0);

    LV_LOG_USER("Pump H-bridge init OK — IN1=GPIO%d IN2=GPIO%d ENA=GPIO%d (%d Hz)",
                PUMP_IN1_PIN, PUMP_IN2_PIN, PUMP_ENA_PIN, PUMP_LEDC_FREQ_HZ);
}

/**
 * Run pump in specified direction at given speed.
 * @param forward  true = filling (IN1=H, IN2=L), false = draining (IN1=L, IN2=H)
 * @param duty     0-255 speed (8-bit). Capped at 250 (~98% max duty for DBH-12V safety)
 */
static void pump_run(bool forward, uint8_t duty)
{
    if (duty > 250) duty = 250;  /* DBH-12V: max 98% duty cycle */
    /* Apply user inversion setting to compensate for physical pump switch */
    if (gui.page.settings.settingsParams.invertPump) forward = !forward;
    gpio_set_level(PUMP_IN1_PIN, forward ? 1 : 0);
    gpio_set_level(PUMP_IN2_PIN, forward ? 0 : 1);
    ledc_set_duty(PUMP_LEDC_MODE, PUMP_LEDC_CHANNEL, duty);
    ledc_update_duty(PUMP_LEDC_MODE, PUMP_LEDC_CHANNEL);
    LV_LOG_USER("Pump: %s duty=%d", forward ? "FORWARD" : "REVERSE", duty);
}

/** Stop the pump (coast stop — both LOW) */
static void pump_stop(void)
{
    ledc_set_duty(PUMP_LEDC_MODE, PUMP_LEDC_CHANNEL, 0);
    ledc_update_duty(PUMP_LEDC_MODE, PUMP_LEDC_CHANNEL);
    gpio_set_level(PUMP_IN1_PIN, 0);
    gpio_set_level(PUMP_IN2_PIN, 0);
    LV_LOG_USER("Pump: STOPPED");
}

#else
/* Simulator stubs */
static void pump_ledc_init(void) { LV_LOG_USER("Pump H-bridge init (stub)"); }
static void pump_run(bool forward, uint8_t duty) {
    /* Mirror real behaviour so the invert setting can be tested in the simulator */
    if (gui.page.settings.settingsParams.invertPump) forward = !forward;
    LV_LOG_USER("Pump: %s duty=%d (stub)", forward ? "FORWARD" : "REVERSE", duty);
}
static void pump_stop(void) { LV_LOG_USER("Pump: STOPPED (stub)"); }
#endif /* BOARD_SIMULATOR */

/* Map an arbitrary pump-speed percentage (10-100%) to H-bridge duty (PUMP_MIN..PUMP_MAX).
 * Public so the speed-tuning popup can drive a live test at any selected value. */
uint8_t pumpPercentToDuty(uint8_t pct)
{
    if (pct < 10)  pct = 10;
    if (pct > 100) pct = 100;
    return (uint8_t)(((uint16_t)(pct - 10) * (PUMP_MAX_ANALOG_VAL - PUMP_MIN_ANALOG_VAL)) / 90
                     + PUMP_MIN_ANALOG_VAL);
}

/* Map the saved pump-speed setting to duty. */
static uint8_t pumpSpeedToDuty(void)
{
    return pumpPercentToDuty(gui.page.settings.settingsParams.pumpSpeed);
}

void rebootBoard(void) {
	sd_log_shutdown();     /* flush + close the SD boot log before restarting */
	esp_restart();
};

/* Put a system request in the queue returns true if successful false if queue is full */
uint8_t qSysAction( uint16_t msg ) {
  
  return xQueueSend( sys.sysActionQ, &msg, 0 );
}

/* Put a motor request in the queue returns true if successful false if queue is full */
uint8_t qMotorAction( uint16_t msg ) {
  
  return xQueueSend( sys.motorActionQ, &msg, 0 );
}


void event_cb(lv_event_t * e) {
	
  lv_obj_t * obj = (lv_obj_t *)lv_event_get_target(e);
  lv_obj_t * objCont = (lv_obj_t *)lv_obj_get_parent(obj);
  lv_obj_t * mboxCont = (lv_obj_t *)lv_obj_get_parent(objCont);

    //const char *label = lv_msgbox_get_active_btn(mbox);
    //LV_UNUSED(label);
    lv_msgbox_close(mboxCont);
    //lv_obj_delete(mboxCont);
    //LV_LOG_USER("Button %s clicked", lv_label_get(label));
}

lv_obj_t * create_radiobutton(lv_obj_t * mBoxParent, const char * txt, const int32_t x, const int32_t y, const int32_t size, const lv_font_t * font, const lv_color_t borderColor, const lv_color_t bgColor) {
	
    lv_obj_t * obj = (lv_obj_t *)lv_checkbox_create(mBoxParent);
    lv_obj_add_flag(obj, LV_OBJ_FLAG_EVENT_BUBBLE);
    lv_obj_set_style_text_font(obj, font, LV_PART_MAIN);
    lv_checkbox_set_text(obj, txt);
    lv_obj_align(obj, LV_ALIGN_RIGHT_MID, x, y);


    int32_t font_h = lv_font_get_line_height(font);
    int32_t pad = (size - font_h) / 2;
    lv_obj_set_style_pad_left(obj, pad, LV_PART_INDICATOR);
    lv_obj_set_style_pad_right(obj, pad, LV_PART_INDICATOR);
    lv_obj_set_style_pad_top(obj, pad, LV_PART_INDICATOR);
    lv_obj_set_style_pad_bottom(obj, pad, LV_PART_INDICATOR);

  lv_obj_set_style_border_color(obj, borderColor, LV_PART_INDICATOR | LV_STATE_DEFAULT);
  lv_obj_set_style_border_color(obj, borderColor, LV_PART_INDICATOR | LV_STATE_CHECKED);
  lv_obj_set_style_bg_color(obj, bgColor, LV_PART_INDICATOR | LV_STATE_CHECKED);

    lv_obj_update_layout(obj);
    return obj;
}

void createMessageBox(lv_obj_t * messageBox, char *title, char *text, char *button1Text, char *button2Text) {
    
    messageBox = lv_msgbox_create(NULL);
    lv_msgbox_add_title(messageBox, title);
    lv_obj_set_style_bg_color(messageBox, lv_palette_main(LV_PALETTE_YELLOW), LV_PART_MAIN);
    //lv_msgbox_add_header_button(messageBox, NULL);
    lv_msgbox_add_text(messageBox, text); 
    

    lv_obj_t * btn;
    btn = lv_msgbox_add_footer_button(messageBox, button1Text);
    lv_obj_add_event_cb(btn, event_cb, LV_EVENT_CLICKED, NULL);
    btn = lv_msgbox_add_footer_button(messageBox, button2Text);
    lv_obj_add_event_cb(btn, event_cb, LV_EVENT_CLICKED, NULL);
    
}

void event_checkbox_handler(lv_event_t * e) {
	
    lv_event_code_t code = lv_event_get_code(e);
    lv_obj_t * obj = (lv_obj_t *)lv_event_get_target(e);
    if(code == LV_EVENT_VALUE_CHANGED) {
        LV_UNUSED(obj);
        const char * txt = lv_checkbox_get_text(obj);
        const char * state = lv_obj_get_state(obj) & LV_STATE_CHECKED ? "Checked" : "Unchecked";
        LV_UNUSED(txt);
        LV_UNUSED(state);
        LV_LOG_USER("%s: %s", txt, state);
    }
}

/*--------------------------------------------------------------
 *  Keyboard context — captured once on CLICKED, reused by
 *  DEFOCUSED / CANCEL / READY so we never re-derive from globals.
 *-------------------------------------------------------------*/
static sKeyboardOwnerContext kbCtx = {0};

static void kb_ctx_clear(void) {
    memset(&kbCtx, 0, sizeof(kbCtx));
}

void kb_ctx_set(const sKeyboardOwnerContext *ctx) {
    kbCtx = *ctx;
}

static const char *kb_owner_name(kbOwnerType owner) __attribute__((unused));
static const char *kb_owner_name(kbOwnerType owner) {
    switch(owner) {
        case KB_OWNER_FILTER: return "filter";
        case KB_OWNER_PROCESS: return "process";
        case KB_OWNER_STEP: return "step";
        case KB_OWNER_SETTINGS: return "settings";
        default: return "unknown";
    }
}

static void kb_commit_text(const char *kbText) {
    if(kbText == NULL || kbCtx.owner == KB_OWNER_NONE) {
        return;
    }

    if(kbCtx.textArea != NULL) {
        lv_textarea_set_text(kbCtx.textArea, kbText);
    }

    switch(kbCtx.owner) {
        case KB_OWNER_FILTER:
            LV_LOG_USER("Press ok from filterPopup");
            snprintf(gui.element.filterPopup.filterName,
                     sizeof(gui.element.filterPopup.filterName), "%s", kbText);
            break;

        case KB_OWNER_PROCESS:
            if(kbCtx.ownerData != NULL) {
                sProcessDetail *pd = (sProcessDetail *)kbCtx.ownerData;
                LV_LOG_USER("Press ok from processDetailNameTextArea");
                if (strcmp(pd->data.processNameString, kbText) != 0) {
                    snprintf(pd->data.processNameString, sizeof(pd->data.processNameString), "%s", kbText);
                    pd->data.somethingChanged = true;
                }
            }
            break;

        case KB_OWNER_STEP:
            if(kbCtx.ownerData != NULL) {
                sStepDetail *sd = (sStepDetail *)kbCtx.ownerData;
                LV_LOG_USER("Press ok from stepDetailNameTextArea");
                if (strcmp(sd->data.stepNameString, kbText) != 0) {
                    snprintf(sd->data.stepNameString, sizeof(sd->data.stepNameString), "%s", kbText);
                    sd->data.somethingChanged = true;
                }
            }
            break;

        case KB_OWNER_SETTINGS:
            /* Wi-Fi password entered from popup */
            LV_LOG_USER("Wi-Fi password entered from keyboard");
            snprintf(gui.element.wifiPopup.pendingPassword,
                     sizeof(gui.element.wifiPopup.pendingPassword), "%s", kbText);
            break;

        default:
            return;
    }

    if(kbCtx.saveButton != NULL) {
        lv_obj_send_event(kbCtx.saveButton, LV_EVENT_REFRESH, NULL);
    }
}

void event_keyboard(lv_event_t* e) {

  lv_event_code_t code = lv_event_get_code(e);
  lv_obj_t * obj = (lv_obj_t *)lv_event_get_target(e);

  if(code == LV_EVENT_VALUE_CHANGED) {
      uint32_t btn_id = lv_buttonmatrix_get_selected_button(gui.element.keyboardPopup.keyboard);
      if(btn_id != LV_BUTTONMATRIX_BUTTON_NONE) {
          const char *txt = lv_buttonmatrix_get_button_text(gui.element.keyboardPopup.keyboard, btn_id);
          if(txt != NULL && strcmp(txt, "123") == 0) {
              for(int i = 0; i < 3; i++) lv_textarea_delete_char(gui.element.keyboardPopup.keyboardTextArea);
              lv_keyboard_set_mode(gui.element.keyboardPopup.keyboard, LV_KEYBOARD_MODE_USER_2);
              LV_LOG_USER("Keyboard switched to numbers/symbols");
              return;
          }
          if(txt != NULL && strcmp(txt, "Abc") == 0) {
              for(int i = 0; i < 3; i++) lv_textarea_delete_char(gui.element.keyboardPopup.keyboardTextArea);
              lv_keyboard_set_mode(gui.element.keyboardPopup.keyboard, LV_KEYBOARD_MODE_USER_3);
              LV_LOG_USER("Keyboard switched to lowercase letters");
              return;
          }
          if(txt != NULL && strcmp(txt, LV_SYMBOL_UP) == 0) {
              /* Toggle uppercase ↔ lowercase */
              lv_keyboard_mode_t cur = lv_keyboard_get_mode(gui.element.keyboardPopup.keyboard);
              if(cur == LV_KEYBOARD_MODE_USER_3) {
                  lv_keyboard_set_mode(gui.element.keyboardPopup.keyboard, LV_KEYBOARD_MODE_USER_1);
                  LV_LOG_USER("Keyboard switched to UPPERCASE");
              } else {
                  lv_keyboard_set_mode(gui.element.keyboardPopup.keyboard, LV_KEYBOARD_MODE_USER_3);
                  LV_LOG_USER("Keyboard switched to lowercase");
              }
              return;
          }
      }
      return;
  }

  if(code == LV_EVENT_CLICKED) {
      sKeyboardOwnerContext *ctx = (sKeyboardOwnerContext *)lv_event_get_user_data(e);
      if(ctx != NULL && ctx->textArea == obj) {
          LV_LOG_USER("LV_EVENT_FOCUSED on keyboard-managed textarea");
          kbCtx = *ctx;
          /* Set max length for the keyboard textarea (0 = use default) */
          uint32_t maxLen = kbCtx.maxLength > 0 ? kbCtx.maxLength : MAX_PROC_NAME_LEN;
          lv_textarea_set_max_length(gui.element.keyboardPopup.keyboardTextArea, maxLen);
          showKeyboard(kbCtx.parentScreen, kbCtx.textArea);
      }
      return;
  }

  if(code == LV_EVENT_DEFOCUSED) {
      if(kbCtx.owner != KB_OWNER_NONE && obj == kbCtx.textArea) {
          LV_LOG_USER("LV_EVENT_DEFOCUSED on %s textarea", kb_owner_name(kbCtx.owner));
          hideKeyboard(kbCtx.parentScreen);
      }
      return;
  }

  if(code == LV_EVENT_CANCEL) {
      if(kbCtx.owner != KB_OWNER_NONE) {
          LV_LOG_USER("LV_EVENT_CANCEL on %s textarea", kb_owner_name(kbCtx.owner));
          hideKeyboard(kbCtx.parentScreen);
      }
      return;
  }

  if(code == LV_EVENT_READY) {
      LV_LOG_USER("LV_EVENT_READY PRESSED");
      kb_commit_text(lv_textarea_get_text(gui.element.keyboardPopup.keyboardTextArea));
      hideKeyboard(kbCtx.parentScreen);
  }
}



void create_keyboard() {
		
    gui.element.keyboardPopup.keyBoardParent = lv_obj_class_create_obj(&lv_msgbox_backdrop_class, lv_layer_top());
    lv_obj_class_init_obj(gui.element.keyboardPopup.keyBoardParent);
    lv_obj_remove_flag(gui.element.keyboardPopup.keyBoardParent, LV_OBJ_FLAG_IGNORE_LAYOUT);
    lv_obj_set_size(gui.element.keyboardPopup.keyBoardParent, LV_PCT(100), LV_PCT(100));

    gui.element.keyboardPopup.keyboard = lv_keyboard_create(gui.element.keyboardPopup.keyBoardParent);
    lv_obj_add_event_cb(gui.element.keyboardPopup.keyboard, event_keyboard, LV_EVENT_CLICKED, NULL);
    lv_obj_add_event_cb(gui.element.keyboardPopup.keyboard, event_keyboard, LV_EVENT_DEFOCUSED, NULL);
    lv_obj_add_event_cb(gui.element.keyboardPopup.keyboard, event_keyboard, LV_EVENT_CANCEL, NULL);
    lv_obj_add_event_cb(gui.element.keyboardPopup.keyboard, event_keyboard, LV_EVENT_READY, NULL);
    lv_obj_add_event_cb(gui.element.keyboardPopup.keyboard, event_keyboard, LV_EVENT_VALUE_CHANGED, NULL);
    lv_obj_add_flag(gui.element.keyboardPopup.keyboard, LV_OBJ_FLAG_EVENT_BUBBLE);


    /* ── USER_1 : letter keyboard ── */
    /* ── USER_1 : UPPERCASE letters (default) ── */
    static const char * kb_map[] = {"Q", "W", "E", "R", "T", "Y", "U", "I", "O", "P", " ", "\n",
                                    "A", "S", "D", "F", "G", "H", "J", "K", "L",  " ", "\n",
                                    LV_SYMBOL_UP," ", "Z", "X", "C", "V", "B", "N", "M"," "," ","\n",
                                    LV_SYMBOL_CLOSE, LV_SYMBOL_BACKSPACE,  " ", "123", LV_SYMBOL_OK, NULL
                                   };

    static const lv_buttonmatrix_ctrl_t kb_ctrl[] = {4, 4, 4, 4, 4, 4, 4, 4, 4, 4, LV_BUTTONMATRIX_CTRL_HIDDEN,
                                                     4, 4, 4, 4, 4, 4, 4, 4, 4, LV_BUTTONMATRIX_CTRL_HIDDEN,
                                                     2, LV_BUTTONMATRIX_CTRL_HIDDEN, 4, 4, 4, 4, 4, 4, 4, LV_BUTTONMATRIX_CTRL_HIDDEN, LV_BUTTONMATRIX_CTRL_HIDDEN,
                                                     2, 2, 4, 2, 2
                                                    };

    /* ── USER_3 : lowercase letters ── */
    static const char * kb_map_lower[] = {"q", "w", "e", "r", "t", "y", "u", "i", "o", "p", " ", "\n",
                                          "a", "s", "d", "f", "g", "h", "j", "k", "l",  " ", "\n",
                                          LV_SYMBOL_UP," ", "z", "x", "c", "v", "b", "n", "m"," "," ","\n",
                                          LV_SYMBOL_CLOSE, LV_SYMBOL_BACKSPACE,  " ", "123", LV_SYMBOL_OK, NULL
                                         };

    static const lv_buttonmatrix_ctrl_t kb_ctrl_lower[] = {4, 4, 4, 4, 4, 4, 4, 4, 4, 4, LV_BUTTONMATRIX_CTRL_HIDDEN,
                                                           4, 4, 4, 4, 4, 4, 4, 4, 4, LV_BUTTONMATRIX_CTRL_HIDDEN,
                                                           2, LV_BUTTONMATRIX_CTRL_HIDDEN, 4, 4, 4, 4, 4, 4, 4, LV_BUTTONMATRIX_CTRL_HIDDEN, LV_BUTTONMATRIX_CTRL_HIDDEN,
                                                           2, 2, 4, 2, 2
                                                          };

    /* ── USER_2 : number / symbol keyboard ── */
    static const char * kb_map_num[] = {"1", "2", "3", "4", "5", "6", "7", "8", "9", "0", " ", "\n",
                                        "-", "/", ":", ";", "(", ")", ".", ",", "@", " ", "\n",
                                        " ", " ", "#", "!", "?", "'", "+", "=", "%", " ", " ", "\n",
                                        LV_SYMBOL_CLOSE, LV_SYMBOL_BACKSPACE, " ", "Abc", LV_SYMBOL_OK, NULL
                                       };

    static const lv_buttonmatrix_ctrl_t kb_ctrl_num[] = {4, 4, 4, 4, 4, 4, 4, 4, 4, 4, LV_BUTTONMATRIX_CTRL_HIDDEN,
                                                         4, 4, 4, 4, 4, 4, 4, 4, 4, LV_BUTTONMATRIX_CTRL_HIDDEN,
                                                         LV_BUTTONMATRIX_CTRL_HIDDEN, LV_BUTTONMATRIX_CTRL_HIDDEN, 4, 4, 4, 4, 4, 4, 4, LV_BUTTONMATRIX_CTRL_HIDDEN, LV_BUTTONMATRIX_CTRL_HIDDEN,
                                                         2, 2, 4, 2, 2
                                                        };

    lv_keyboard_set_map(gui.element.keyboardPopup.keyboard, LV_KEYBOARD_MODE_USER_1, kb_map, kb_ctrl);
    lv_keyboard_set_map(gui.element.keyboardPopup.keyboard, LV_KEYBOARD_MODE_USER_2, kb_map_num, kb_ctrl_num);
    lv_keyboard_set_map(gui.element.keyboardPopup.keyboard, LV_KEYBOARD_MODE_USER_3, kb_map_lower, kb_ctrl_lower);
    lv_keyboard_set_mode(gui.element.keyboardPopup.keyboard, LV_KEYBOARD_MODE_USER_3);
    
    const ui_keyboard_layout_t *kb = &ui_get_profile()->keyboard;
    gui.element.keyboardPopup.keyboardTextArea = lv_textarea_create(gui.element.keyboardPopup.keyBoardParent);
    lv_obj_align(gui.element.keyboardPopup.keyboardTextArea, LV_ALIGN_TOP_MID, 0, kb->textarea_y);
    lv_textarea_set_placeholder_text(gui.element.keyboardPopup.keyboardTextArea, keyboard_placeholder_text);
    lv_obj_set_size(gui.element.keyboardPopup.keyboardTextArea, lv_pct(90), kb->textarea_h);
    lv_obj_add_state(gui.element.keyboardPopup.keyboardTextArea, LV_STATE_FOCUSED);
    lv_textarea_set_max_length(gui.element.keyboardPopup.keyboardTextArea, MAX_PROC_NAME_LEN);
    lv_keyboard_set_textarea(gui.element.keyboardPopup.keyboard, gui.element.keyboardPopup.keyboardTextArea);

    lv_obj_set_style_text_font(gui.element.keyboardPopup.keyboard, kb->keyboard_font, 0);
    lv_obj_set_style_text_font(gui.element.keyboardPopup.keyboardTextArea, kb->textarea_font, 0);
    
    lv_obj_add_flag(gui.element.keyboardPopup.keyBoardParent, LV_OBJ_FLAG_HIDDEN);
}


lv_obj_t * create_text(lv_obj_t * parent, const char * icon, const char * txt) {
	
    lv_obj_t * obj =  (lv_obj_t *)lv_menu_cont_create(parent);

    lv_obj_t * img = NULL;
    lv_obj_t * label = NULL;

    if(icon) {
        img = lv_image_create(obj);
        lv_image_set_src(img, icon);
        //lv_obj_set_size(img, 46, 46);
    }

    if(txt) {
        label = lv_label_create(obj);
        lv_label_set_text(label, txt);
        lv_label_set_long_mode(label, LV_LABEL_LONG_SCROLL_CIRCULAR);
        lv_obj_set_flex_grow(label, 1);
        lv_obj_align(label, LV_ALIGN_OUT_BOTTOM_MID, 0, 0);
    }


    return obj;
}


lv_obj_t * create_slider(lv_obj_t * parent, const char * icon, const char * txt, int32_t min, int32_t max, int32_t val) {
	
    lv_obj_t * obj =  (lv_obj_t *) create_text(parent, icon, txt);

    lv_obj_t * slider =  (lv_obj_t *) lv_slider_create(obj);
    lv_obj_set_flex_grow(slider, 1);
    lv_slider_set_range(slider, min, max);
    lv_slider_set_value(slider, val, LV_ANIM_OFF);

    if(icon == NULL) {
        lv_obj_add_flag(slider, LV_OBJ_FLAG_FLEX_IN_NEW_TRACK);
    }

    return obj;
}

lv_obj_t * create_switch(lv_obj_t * parent, const char * icon, const char * txt, bool chk) {
	
    lv_obj_t * obj =  (lv_obj_t *) create_text(parent, icon, txt);

    lv_obj_t * sw = (lv_obj_t *)lv_switch_create(obj);
    lv_obj_add_state(sw, chk ? LV_STATE_CHECKED : 0);

    return obj;
}


void createQuestionMark(lv_obj_t * parent, lv_obj_t * element, lv_event_cb_t e, const int32_t x, const int32_t y)
{
    lv_obj_t *questionMark = lv_label_create(parent);

    #if (LCD_H_RES == 480) && (LCD_V_RES == 320)
        const lv_font_t *qm_font = &FilMachineFontIcons_15;
    #else
        const lv_font_t *qm_font = &FilMachineFontIcons_30;
    #endif

    int32_t sz = (int32_t)((lv_font_get_line_height(qm_font) * 3) / 2);

    lv_obj_set_size(questionMark, sz, sz);
    lv_label_set_text(questionMark, questionMark_icon);
    lv_obj_add_event_cb(questionMark, e, LV_EVENT_CLICKED, element);
    lv_obj_set_style_text_font(questionMark, qm_font, 0);
    lv_obj_align_to(questionMark, element, LV_ALIGN_OUT_RIGHT_MID, x, y);
    lv_obj_add_flag(questionMark, LV_OBJ_FLAG_CLICKABLE);
}

void createPopupBackdrop(lv_obj_t **parent, lv_obj_t **container, int32_t width, int32_t height) {
    *parent = lv_obj_class_create_obj(&lv_msgbox_backdrop_class, lv_layer_top());
    lv_obj_class_init_obj(*parent);
    lv_obj_remove_flag(*parent, LV_OBJ_FLAG_IGNORE_LAYOUT);
    lv_obj_set_size(*parent, LV_PCT(100), LV_PCT(100));

    *container = lv_obj_create(*parent);
    lv_obj_align(*container, LV_ALIGN_CENTER, 0, 0);
    lv_obj_set_size(*container, width, height);
    lv_obj_remove_flag(*container, LV_OBJ_FLAG_SCROLLABLE);
}

void initTitleLineStyle(lv_style_t *style, uint32_t color) {
    lv_style_init(style);
    lv_style_set_line_width(style, ui_get_profile()->title_line_width);
    lv_style_set_line_color(style, lv_color_hex(color));
    lv_style_set_line_rounded(style, true);
}

int32_t convertCelsiusToFahrenheit( int32_t tempC ) {
  return (int32_t)((float)tempC * 1.8 + 32 + 0.5); // Add 0.5 for rounding
}

uint32_t calc_buf_len( uint32_t maxVal, uint8_t extra_len ) {
    uint8_t caseVal = LESS_THAN_10;
    uint32_t len = 0, remainder = maxVal;
    
    if( maxVal > 999 ) return 0; // Limit to 999 although this is alot!
    if( maxVal > 99 ) caseVal = GREATER_THAN_99;
    else if( maxVal > 9 ) caseVal = GREATER_THAN_9;
    switch( caseVal ) {
        case GREATER_THAN_99:
          len += ( (4 + extra_len) * (remainder - 99)); // Add storage length for the 3 digit numbers + a '\n' charater
          remainder -= (remainder - 99); // Deduct what we have accounted for so far
          /* FALLTHRU */
        case GREATER_THAN_9: // Fall through case (no break; required!)
          len += ( (3 + extra_len) * (remainder - 9)); // Add the storage length for the 2 digit numbers + a '\n' character
          remainder -= (remainder - 9); // Deduct what we have accounted for so far
          /* FALLTHRU */
        case LESS_THAN_10:
        default:
          len +=( (2 + extra_len) * remainder); // Add strorage length for the 1 digit numbers + a '\n'
          remainder -= remainder; // Deduct what we have finally accounted for... Remainder should now be zero!
        break;
        }
    if( !remainder ) {
        return len; // All well return length
    } else {
        return 0; // Something went wrong, so we return 0 length for buffer to show error!
    }
}

char *createRollerValues(uint32_t minVal, uint32_t maxVal, const char* extra_str, bool isFahrenheit) {
    // Calculate the required buffer length
    uint32_t buf_len = 0;
    for (uint32_t i = minVal; i <= maxVal; i++) {
        int value = isFahrenheit ? convertCelsiusToFahrenheit(i) : i;
        buf_len += snprintf(NULL, 0, "%s%d\n", extra_str, value);
    }
    buf_len -= 1; // Remove the last newline to avoid empty space

    // Allocate memory for the buffer
    char *buf = (char *)malloc(buf_len + 1); // +1 for null terminator
    if (!buf) {
        return NULL; // Handle malloc failure
    }

    // Popola il buffer con i valori
    uint32_t buf_ptr = 0;
    for (uint32_t i = minVal; i <= maxVal; i++) {
        int value = isFahrenheit ? convertCelsiusToFahrenheit( i ) : i;
        if (i == maxVal) {
            buf_ptr += snprintf(&buf[buf_ptr], (buf_len - buf_ptr + 1), "%s%d", extra_str, value);
        } else {
            buf_ptr += snprintf(&buf[buf_ptr], (buf_len - buf_ptr + 1), "%s%d\n", extra_str, value);
        }
    }
    return buf;
}
void myLongEvent(lv_event_t * e, uint32_t howLongInMs) {
	
    lv_event_code_t code = lv_event_get_code(e);
    static uint32_t t;
    if(code == LV_EVENT_PRESSED) {
        t = lv_tick_get();
    } 
    else if(code == LV_EVENT_PRESSING) {
        if(lv_tick_elaps(t) > howLongInMs) {
            /*Do something*/
        }
    }
}

void* allocateAndInitializeNode(NodeType_t type) {
    void *node = NULL;

    // Initialize and allocate according to the node type
    switch (type) {
        case STEP_NODE:
            node = heap_caps_malloc(sizeof(stepNode), MALLOC_CAP_SPIRAM);
            if (node != NULL) {
                memset(node, 0, sizeof(stepNode));
                stepNode* step = (stepNode*)node;
                step->step.stepDetails = (sStepDetail *)heap_caps_malloc(sizeof(sStepDetail), MALLOC_CAP_SPIRAM);
                if (step->step.stepDetails == NULL) {
                    // Handle memory allocation failure
                    free(step);
                    return NULL;
                }
                memset(step->step.stepDetails, 0, sizeof(sStepDetail));
            } else {
                // Handle memory allocation failure
                return NULL;
            }
            break;

        case PROCESS_NODE:
            node = heap_caps_malloc(sizeof(processNode), MALLOC_CAP_SPIRAM);
            if (node != NULL) {
                memset(node, 0, sizeof(processNode));
                processNode* process = (processNode*)node;
                process->process.processDetails = (sProcessDetail *)heap_caps_malloc(sizeof(sProcessDetail), MALLOC_CAP_SPIRAM);
                if (process->process.processDetails == NULL) {
                    // Handle memory allocation failure
                    free(process);
                    return NULL;
                }
                memset(process->process.processDetails, 0, sizeof(sProcessDetail));

                process->process.processDetails->checkup = (sCheckup *)heap_caps_malloc(sizeof(sCheckup), MALLOC_CAP_SPIRAM);
                if (process->process.processDetails->checkup == NULL) {
                    // Handle memory allocation failure
                    free(process->process.processDetails);
                    free(process);
                    return NULL;
                }
                memset(process->process.processDetails->checkup, 0, sizeof(sCheckup));
                process->process.processDetails->checkup->data.tankSize = gui.page.settings.settingsParams.tankSize > 0 ? gui.page.settings.settingsParams.tankSize : 2;
            } else {
                // Handle memory allocation failure
                return NULL;
            }
            break;

        default:
            // Handle invalid node type
            return NULL;
    }

    return node;
}

void* isNodeInList(void* list, void* node, NodeType_t type) {
    if (list == NULL || node == NULL) {
        return NULL;
    }

    switch (type) {
        case STEP_NODE: {
            stepList* sList = (stepList*)list;
            stepNode* current = sList->start;

            while (current != NULL) {
                if (current == (stepNode*)node) {
                    return (void*)current;  // Node found
                }
                current = current->next;
            }
            break;
        }

        case PROCESS_NODE: {
            processList* pList = (processList*)list;
            processNode* current = pList->start;

            while (current != NULL) {
                if (current == (processNode*)node) {
                    return (void*)current;  // Node found
                }
                current = current->next;
            }
            break;
        }
    }

    // Node not found
    return NULL;
}



void initGlobals( void ) {
  // Initialise the main GUI & sys structures to zero
  memset(&gui, 0, sizeof(gui));
  memset(&sys, 0, sizeof(sys));
  
  //gui.page.processes.processElementsList.start = NULL;  // Not rquired memset above does this only need to set non-zero values ( NULL is also zero )
  //gui.page.processes.processElementsList.end   = NULL;
  //gui.page.processes.processElementsList.size  = 0;

  // We only need to initialise the non-zero values
  const ui_profile_t *ui = ui_get_profile();
  gui.element.cleanPopup.titleLinePoints[1].x = ui->popups.clean_title_line_w;
    gui.element.drainPopup.titleLinePoints[1].x = ui->popups.drain_title_line_w;
    gui.element.selfcheckPopup.titleLinePoints[1].x = ui->popups.selfcheck_title_line_w;
    gui.element.filterPopup.titleLinePoints[1].x = ui->popups.filter_title_line_w;
    gui.element.rollerPopup.titleLinePoints[1].x = ui->popups.roller_title_line_w;
    gui.element.messagePopup.titleLinePoints[1].x = ui->popups.message_title_line_w;

    gui.page.processes.titleLinePoints[1].x = ui->common.title_line_w;
    gui.page.settings.titleLinePoints[1].x = ui->common.title_line_w;
    gui.page.tools.titleLinePoints[1].x = ui->common.title_line_w;
  
  /* Sensible defaults for settings (overridden by config file if present) */
  gui.page.settings.settingsParams.tankSize = 2;           /* Medium */
  gui.page.settings.settingsParams.pumpSpeed = 30;
  gui.page.settings.settingsParams.invertPump = false;
  gui.page.settings.settingsParams.chemCalibOffset = 0;
  gui.page.settings.settingsParams.chemCalibFillSecs = 0;   /* uncalibrated (was chemContainerMl) */
  gui.page.settings.settingsParams.wbCalibFillSecs = 0;     /* uncalibrated (was wbContainerMl) */
  gui.page.settings.settingsParams.volume = 60;
  gui.page.settings.settingsParams.chemistryVolume = 2;    /* High */
  gui.page.settings.settingsParams.filmRotationSpeedSetpoint = 50;
  sys.analogVal_rotationSpeedPercent = mapPercentageToValue(50, 10, 100);
  gui.page.settings.settingsParams.rotationIntervalSetpoint = 10;
  gui.page.settings.settingsParams.multiRinseTime = 60;
  gui.page.settings.settingsParams.drainFillOverlapSetpoint = 100;
  gui.page.settings.settingsParams.lineRinseEnabled = false;   /* opt-in */
  gui.page.settings.settingsParams.lineRinseTime = 10;         /* seconds */
  gui.page.settings.settingsParams.language = LANG_EN;         /* English default */
  gui.page.settings.settingsParams.screenOffMins = 10;        /* screen off after 10 min */
  filmLoaderApplyDefaults(&gui.page.settings.settingsParams); /* loader speed + cutter servo */

  gui.element.rollerPopup.tempCelsiusOptions = createRollerValues(TEMP_ROLLER_MIN,TEMP_ROLLER_MAX,"",false);
  gui.element.rollerPopup.tempFahrenheitOptions = createRollerValues(TEMP_ROLLER_MIN,TEMP_ROLLER_MAX,"",true);
  gui.element.rollerPopup.minutesOptions = createRollerValues(0,240,"",false);
  gui.element.rollerPopup.secondsOptions = createRollerValues(0,59,"",false); 
  /* Fixed tolerance values matching Flutter: ±0.3°, ±0.5°, ±1.0° */
  {
      const char *tol = "0.3\n0.5\n1.0";
      gui.element.rollerPopup.tempToleranceOptions = strdup(tol);
  }

  //gui.element.filterPopup.filterName = ""; // Not Required this will set this to some constant pointer which is not good...
  //gui.element.filterPopup.isColorFilter = FILM_TYPE_NA;   // This breaks filtering not needed
  //gui.element.filterPopup.isBnWFilter = FILM_TYPE_NA;
  //gui.element.filterPopup.isBnWFilter = 0;
  //gui.element.filterPopup.preferredOnly = 0;
  
  //gui.page.processes.isFiltered = 0; // Not Required memset takes care of this also

  gui.tempProcessNode = (processNode*) allocateAndInitializeNode(PROCESS_NODE);
  if (gui.tempProcessNode == NULL) {
      LV_LOG_USER("Failed to allocate tempProcessNode");
  }
  gui.tempStepNode = (stepNode*) allocateAndInitializeNode(STEP_NODE);
  if (gui.tempStepNode == NULL) {
      LV_LOG_USER("Failed to allocate tempStepNode");
  }

}

//without the commented part, the keyboard will be shown OVER the caller
void showKeyboard(lv_obj_t * whoCallMe, lv_obj_t * textArea){
    if(textArea != NULL){
    //lv_obj_add_flag(whoCallMe, LV_OBJ_FLAG_HIDDEN);
      if(strlen(lv_textarea_get_text(textArea)) > 0)
        lv_textarea_set_text(gui.element.keyboardPopup.keyboardTextArea, lv_textarea_get_text(textArea));
      else
        lv_textarea_set_text(gui.element.keyboardPopup.keyboardTextArea, "");

      lv_keyboard_set_mode(gui.element.keyboardPopup.keyboard, LV_KEYBOARD_MODE_USER_3);
      lv_obj_remove_flag(gui.element.keyboardPopup.keyBoardParent, LV_OBJ_FLAG_HIDDEN);
      lv_obj_move_foreground(gui.element.keyboardPopup.keyBoardParent);
    } else lv_textarea_set_text(gui.element.keyboardPopup.keyboardTextArea, "");
}

void hideKeyboard(lv_obj_t * whoCallMe){
    LV_UNUSED(whoCallMe);
    lv_obj_add_flag(gui.element.keyboardPopup.keyBoardParent, LV_OBJ_FLAG_HIDDEN);
    lv_obj_move_background(gui.element.keyboardPopup.keyBoardParent);
    lv_textarea_set_text(gui.element.keyboardPopup.keyboardTextArea, "");
    kb_ctx_clear();
}

/* SD boot-log hooks — the strong versions live in sd_log.c (firmware only);
 * these weak no-ops keep the simulator linking. */
void __attribute__((weak)) sd_log_line(const char *line) { (void)line; }
void __attribute__((weak)) sd_log_shutdown(void) { }

#if LV_USE_LOG != 0
void my_print( lv_log_level_t level, const char * buf )
{
    LV_UNUSED(level);
    printf( "%s\r\n", buf );
    sd_log_line(buf);          /* tee every LV_LOG line to the SD boot log */
}
#endif

uint8_t SD_init() {

    sdmmc_card_t *card;
    esp_vfs_fat_sdmmc_mount_config_t mount = {
        .format_if_mount_failed = false,
        .max_files = 5,
    };
    LV_LOG_USER("Initialise SD Card");

#if defined(SD_BUS_SDMMC)
    /* ── P4: SDMMC 4-bit bus (much faster than SPI) ──
     * The JC4880P433 board requires on-chip LDO channel 4 (3.3V)
     * to power the SD card slot — without it the card won't respond.
     * (Same pattern used by RetroESP32-P4 reference project.)
     */

    /* 1. Power the SD card via on-chip LDO */
    sd_pwr_ctrl_ldo_config_t ldo_config = { .ldo_chan_id = 4 };
    sd_pwr_ctrl_handle_t pwr_ctrl_handle = NULL;
    esp_err_t ldo_ret = sd_pwr_ctrl_new_on_chip_ldo(&ldo_config, &pwr_ctrl_handle);
    if (ldo_ret != ESP_OK) {
        ESP_LOGE(TAG, "Failed to init SD LDO power (ch4): %s", esp_err_to_name(ldo_ret));
    }

    /* 2. Configure SDMMC host — slot 0, default speed for reliable init */
    sdmmc_host_t host = SDMMC_HOST_DEFAULT();
    host.slot = SDMMC_HOST_SLOT_0;
    host.max_freq_khz = SDMMC_FREQ_DEFAULT;
    if (pwr_ctrl_handle) {
        host.pwr_ctrl_handle = pwr_ctrl_handle;
    }

    /* 3. Configure slot pins (4-bit bus) */
    sdmmc_slot_config_t slot_config = SDMMC_SLOT_CONFIG_DEFAULT();
    slot_config.clk = SD_MMC_CLK;
    slot_config.cmd = SD_MMC_CMD;
    slot_config.d0  = SD_MMC_D0;
    slot_config.d1  = SD_MMC_D1;
    slot_config.d2  = SD_MMC_D2;
    slot_config.d3  = SD_MMC_D3;
    slot_config.width = 4;
    slot_config.cd  = SDMMC_SLOT_NO_CD;
    slot_config.wp  = SDMMC_SLOT_NO_WP;
    slot_config.flags |= SDMMC_SLOT_FLAG_INTERNAL_PULLUP;

    /* 4. Mount with retry + power-cycle (some cards need a reset) */
    ESP_LOGI(TAG, "Mounting filesystem (SDMMC 4-bit)");
    esp_err_t mount_ret = ESP_FAIL;
    for (int attempt = 0; attempt < 3; attempt++) {
        mount_ret = esp_vfs_fat_sdmmc_mount("/sd", &host, &slot_config, &mount, &card);
        if (mount_ret == ESP_OK) break;
        ESP_LOGW(TAG, "SD mount attempt %d failed (%s), power-cycling...",
                 attempt + 1, esp_err_to_name(mount_ret));
        vTaskDelay(pdMS_TO_TICKS(500));
    }
    if (mount_ret != ESP_OK) {
        LV_LOG_USER("Card Mount Failed (SDMMC) after 3 attempts");
        return ESP_FAIL;
    }

#else
    /* ── S3: SPI SD card ── */
    sdmmc_host_t host = SDSPI_HOST_DEFAULT();
    host.slot = SDSPI_HOST_ID;

    spi_bus_config_t bus_cfg = {
        .mosi_io_num = SD_MOSI,
        .miso_io_num = SD_MISO,
        .sclk_io_num = SD_SCLK,
        .quadwp_io_num = -1,
        .quadhd_io_num = -1,
        .max_transfer_sz = 4000,
    };

    if (spi_bus_initialize(host.slot, &bus_cfg, SDSPI_DEFAULT_DMA) != ESP_OK) {
        ESP_LOGE(TAG, "Failed to initialise SPI bus.");
        return ESP_FAIL;
    }

    sdspi_device_config_t slot_config = SDSPI_DEVICE_CONFIG_DEFAULT();
    slot_config.gpio_cs = SD_CS;
    slot_config.host_id = host.slot;

    ESP_LOGI(TAG, "Mounting filesystem (SPI)");
    if (esp_vfs_fat_sdspi_mount("/sd", &host, &slot_config, &mount, &card) != ESP_OK) {
        LV_LOG_USER("Card Mount Failed");
        return ESP_FAIL;
    }
#endif

    LV_LOG_USER("SD init okay.");
    sdmmc_card_print_info(stdout, card);
    return ESP_OK;
}

#if defined(BOARD_JC4880P433)
/* Global I2C master bus handle — used by init_touch() in FilMachine.c */
i2c_master_bus_handle_t g_i2c_bus_handle = NULL;
#endif

void init_Pins_and_Buses( void ) {
	
#if defined(DISPLAY_DRIVER_ST7701)
    /* P4: backlight is managed by st7701_lcd via LEDC PWM — skip GPIO init here */
    ESP_LOGI(TAG, "LCD backlight: managed by st7701_lcd (LEDC PWM)");
#else
    ESP_LOGI(TAG, "Turn off LCD backlight");
    gpio_config_t bk_gpio_config = {
        .mode = GPIO_MODE_OUTPUT,
        .pin_bit_mask = 1ULL << LCD_BLK
    };
    ESP_ERROR_CHECK(gpio_config(&bk_gpio_config));
    gpio_set_level(LCD_BLK, LCD_BK_LIGHT_OFF_LEVEL);
#endif

#if defined(DISPLAY_BUS_PARALLEL16)
    ESP_LOGI(TAG, "Set RD Pin High");		/* Required for parallel-16 bus displays */
    gpio_config_t rd_gpio_config = {
        .mode = GPIO_MODE_OUTPUT,
        .pin_bit_mask = 1ULL << LCD_RD
    };
    ESP_ERROR_CHECK(gpio_config(&rd_gpio_config));
    gpio_set_level(LCD_RD, 1);
#endif

	if (SD_init()) {
	    initErrors = INIT_ERROR_SD;
	    LV_LOG_USER("ERROR:   SD initErrors %d", initErrors);
	} else{
//	    createFile(SD, FILENAME_SAVE);
	    LV_LOG_USER("SD INIT OVER initErrors %d", initErrors);
	}

    /* Initialize I2C */
    ESP_LOGI(TAG, "Initialize I2C bus %d (SDA=%d, SCL=%d)", I2C_NUM, I2C_SDA, I2C_SCL);
#if defined(BOARD_JC4880P433)
    /* ESP32-P4: use the new I2C master driver (old API deprecated on P4).
     * The GT911 managed component and MCP23017/PCA9685 still work via
     * the legacy-compatible i2c_master_get_bus_handle() bridge. */
    i2c_master_bus_config_t i2c_bus_cfg = {
        .i2c_port = I2C_NUM,
        .sda_io_num = I2C_SDA,
        .scl_io_num = I2C_SCL,
        .clk_source = I2C_CLK_SRC_DEFAULT,
        .glitch_ignore_cnt = 7,
        .flags.enable_internal_pullup = true,
    };
    ESP_ERROR_CHECK(i2c_new_master_bus(&i2c_bus_cfg, &g_i2c_bus_handle));
#else
    const i2c_config_t i2c_conf = {
        .mode = I2C_MODE_MASTER,
        .sda_io_num = I2C_SDA,
        .scl_io_num = I2C_SCL,
        .sda_pullup_en = GPIO_PULLUP_ENABLE,
        .scl_pullup_en = GPIO_PULLUP_ENABLE,
        .master.clk_speed = 400000,
    };
    ESP_ERROR_CHECK(i2c_param_config(I2C_NUM, &i2c_conf));
    ESP_ERROR_CHECK(i2c_driver_install(I2C_NUM, i2c_conf.mode, 0, 0, 0));
#endif

    /* Initialize MCP23017 I/O expander (Adafruit #6318 solenoid driver) */
    esp_err_t mcp_ret;
#if defined(BOARD_JC4880P433)
    /* The MCP23017 on the #6318 can be left holding SDA low after a P4 soft-reset
     * (the expander itself doesn't reset with the MCU), so the very first probe
     * may NACK -> "not found". Recover the bus and retry a few times before
     * giving up, so valves/heater don't silently drop out on some boots. */
    mcp_ret = ESP_FAIL;
    for (int attempt = 1; attempt <= 3; attempt++) {
        i2c_master_bus_reset(g_i2c_bus_handle);
        vTaskDelay(pdMS_TO_TICKS(20));
        mcp_ret = mcp23017_init(&mcp, g_i2c_bus_handle, MCP23017_DEFAULT_ADDR);
        if (mcp_ret == ESP_OK) break;
        LV_LOG_USER("MCP23017 probe %d/3 failed (0x%x) — bus reset + retry", attempt, mcp_ret);
    }
#else
    mcp_ret = mcp23017_init(&mcp, I2C_NUM, MCP23017_DEFAULT_ADDR);
#endif
    if (mcp_ret != ESP_OK) {
        LV_LOG_USER("MCP23017 init ERROR!");
        initErrors = INIT_ERROR_I2C_MCP;
    } else {
        LV_LOG_USER("MCP23017 init OK at 0x%02X", MCP23017_DEFAULT_ADDR);
        initializeRelayPins();
        initializeMotorPins();
        initializeChemLevelPins();
        /* NOTE: the valve self-test used to run here and blocked boot for
         * ~3.75s before the display came up. It is now deferred: app_main posts
         * SELFTEST_VALVES to sysMan right after the splash loads, so the display
         * appears immediately and the valves cycle in the background. */
    }

#if defined(BOARD_JC4880P433)
    /* I2C bus recovery — ensure SDA/SCL are released before GT911 touch init.
     * MCP23017 transactions at 400kHz can occasionally leave the bus in a bad
     * state (SDA held low). This reset clears any stuck condition so the
     * GT911 touch controller (100kHz) initializes reliably. */
    esp_err_t bus_rst = i2c_master_bus_reset(g_i2c_bus_handle);
    if (bus_rst != ESP_OK) {
        LV_LOG_USER("I2C bus reset warning (0x%x) — GT911 may fail", bus_rst);
    } else {
        LV_LOG_USER("I2C bus reset OK — bus ready for GT911 touch");
    }

    /* ── Audio: ES8311 codec on the shared I2C bus ── */
    if (audio_init(g_i2c_bus_handle) != ESP_OK) {
        LV_LOG_USER("ES8311 audio init FAILED — no sound");
    } else {
        uint8_t vol = gui.page.settings.settingsParams.volume;
        audio_set_volume(vol ? vol : 60);
        LV_LOG_USER("ES8311 audio init OK");
    }
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
